Jimmy-Chu-127/Pinball-Machine-Built-from-Scratch/images/block_diagram_pinball_machine.png

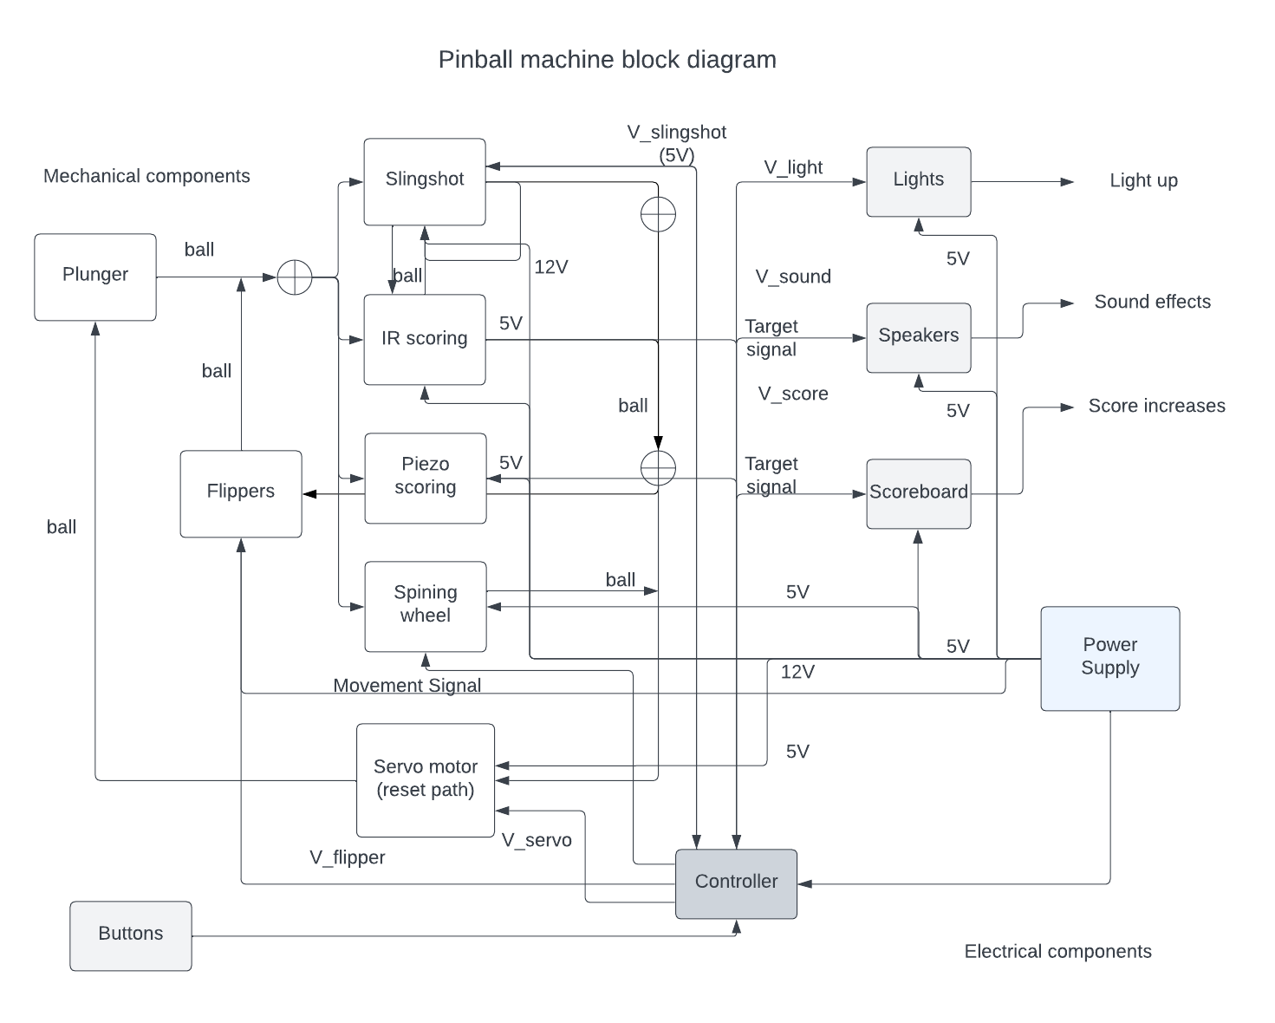
images/block_diagram_pinball_machine.png
