Jimmy-Chu-127/Pinball-Machine-Built-from-Scratch/Module 4/smps-lrs-75-12-1.snapshot.1/SMPS SMALL_LRS-75-12.JPG

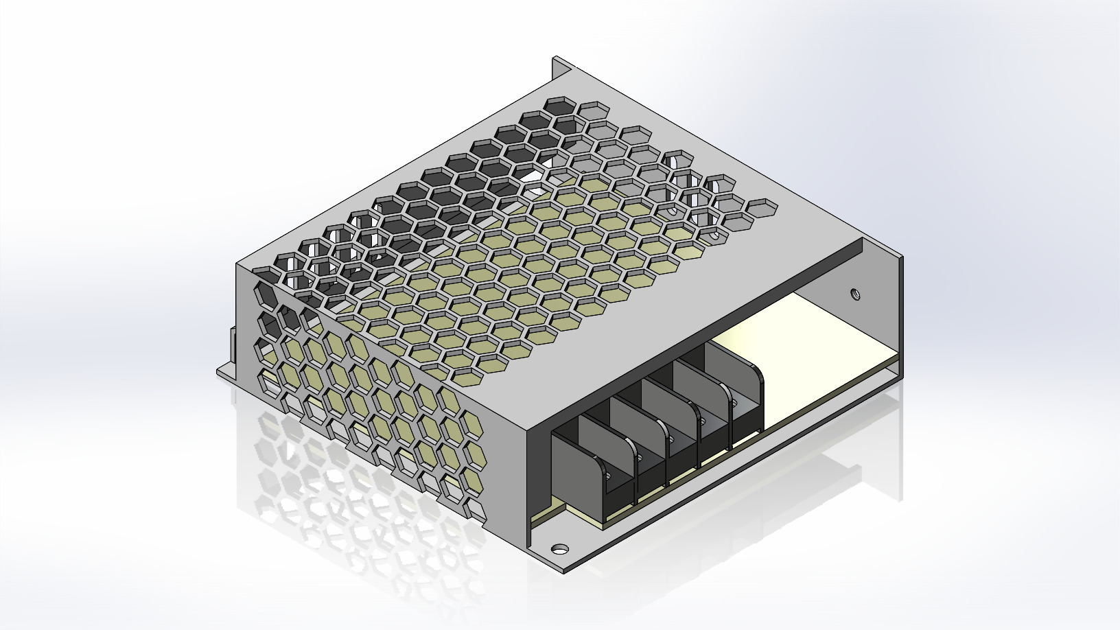
Module 4/smps-lrs-75-12-1.snapshot.1/SMPS SMALL_LRS-75-12.JPG
