Jimmy-Chu-127/Pinball-Machine-Built-from-Scratch/Module 4/switch_button/Rocker switch 3pin_3.JPG

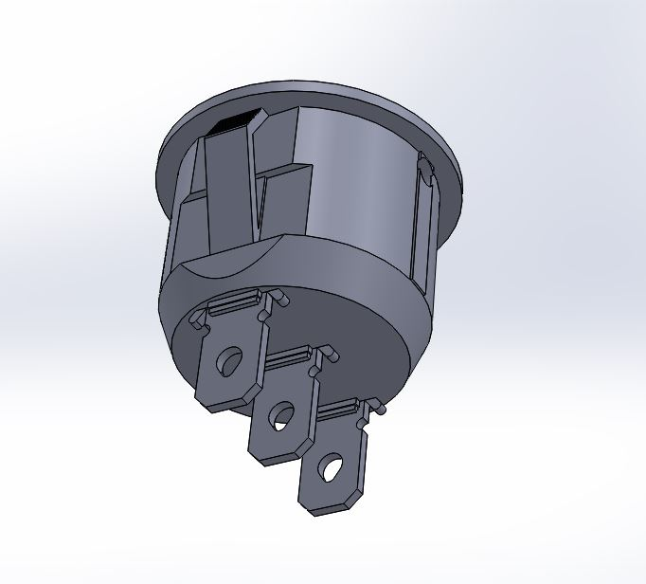
Module 4/switch_button/Rocker switch 3pin_3.JPG
