Jimmy-Chu-127/Pinball-Machine-Built-from-Scratch/Module 2/slingshot assem.SLDASM

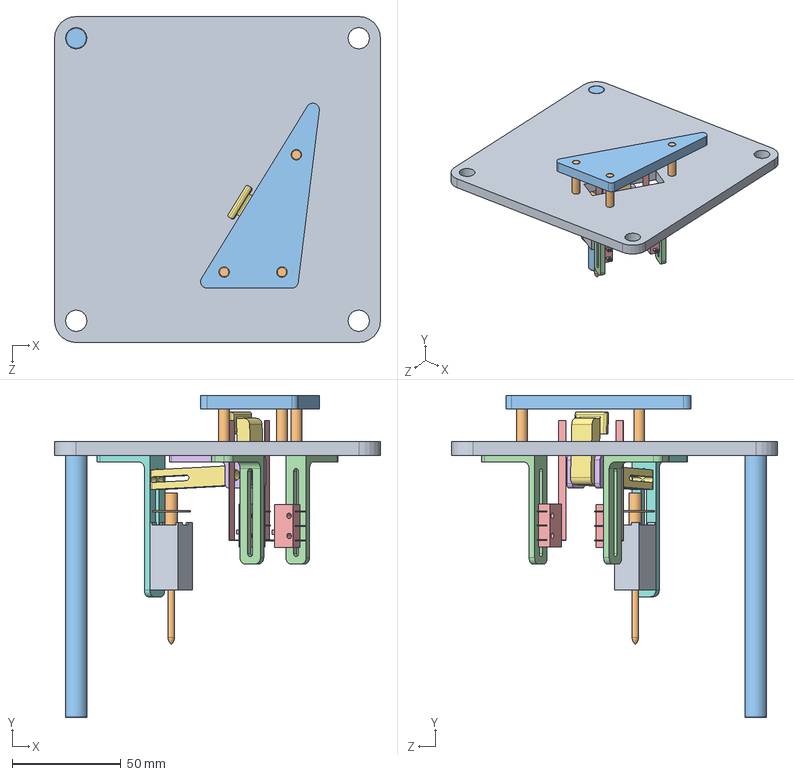
[picture p46: CAD file, 2023-05-12]
Module 2/slingshot assem.SLDASM
150.0 x 148.4 x 150.0 mm
slingshot testbed v2
slingshot support rod x 3
slingshot cover
slingshot limit switch holder x 2
slingshot limit switch x 2
slingshot arm holder
slingshot arm
slingshot solenoid holder vertical
slingshot solenoid body
slingshot solenoid rod
