Jimmy-Chu-127/Pinball-Machine-Built-from-Scratch/Module 1/plunger_assembly1_spring_head_rod.stl

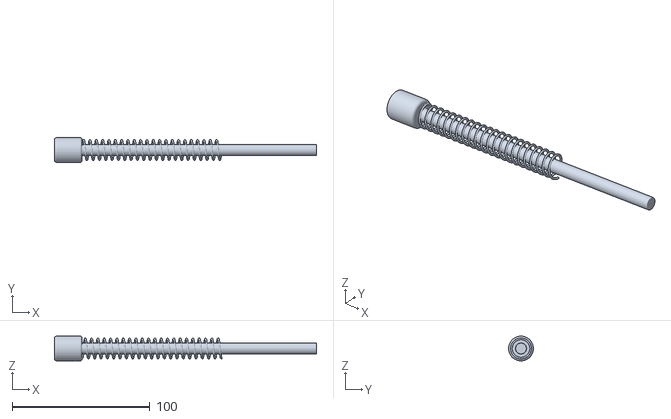
[picture p47: CAD file, 2023-04-08]
Module 1/plunger_assembly1_spring_head_rod.stl
190.0 x 18.0 x 18.0
