Jimmy-Chu-127/Pinball-Machine-Built-from-Scratch/Module 4/AL6M-M14G.SLDASM

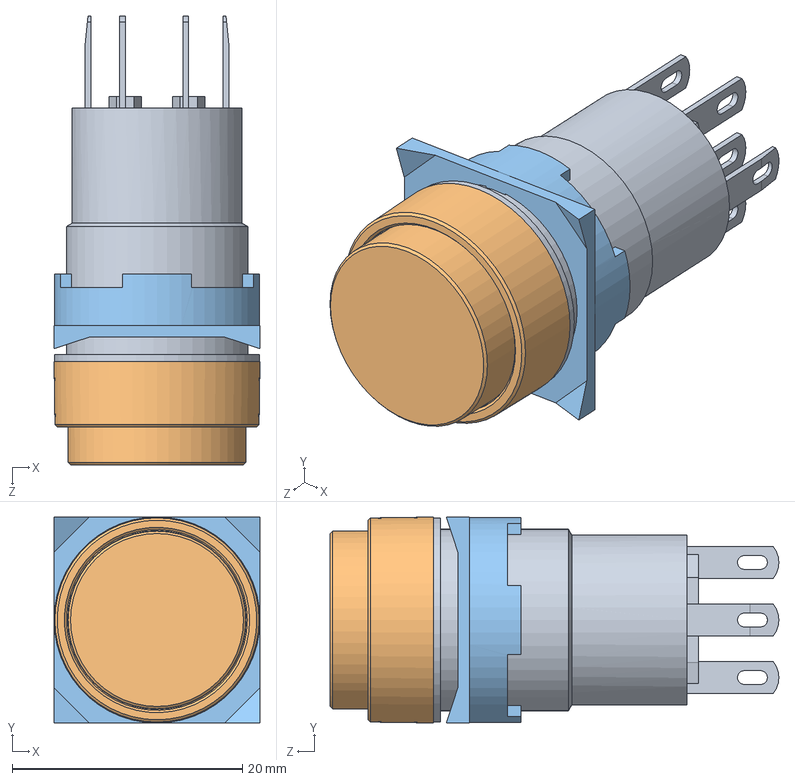
[picture p48: CAD file, 2023-05-24]
Module 4/AL6M-M14G.SLDASM
17.9 x 17.9 x 39.0 mm
AL6M-M14G
_A6LM-M14G_round
_A6LM-M14_nut_set
