Jimmy-Chu-127/Pinball-Machine-Built-from-Scratch/Module 2/flipper_assem1.SLDASM

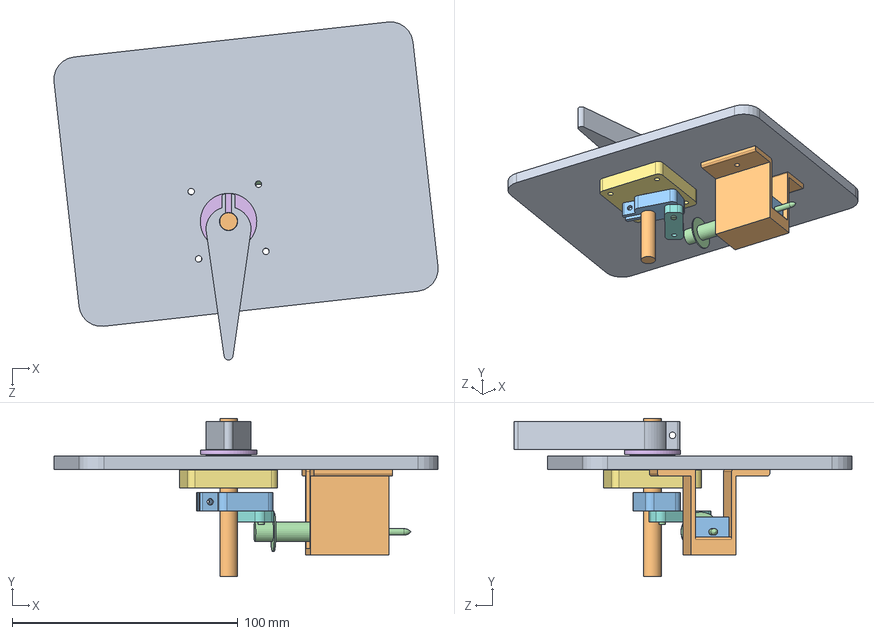
[picture p49: CAD file, 2023-04-26]
Module 2/flipper_assem1.SLDASM
170.1 x 70.0 x 149.7 mm
flipper_part1
flipper_part2
flipper_part3
flipper_part4
flipper_bearing
flipper_washer
flipper_part5
flipper_part6
plane
solenoid_holder
solenoid body
solenoid rod
