Jimmy-Chu-127/Pinball-Machine-Built-from-Scratch/3D printer - Laser cutting/5_21_print/3mf/ECE 115 Playfield spinning wheel.3mf

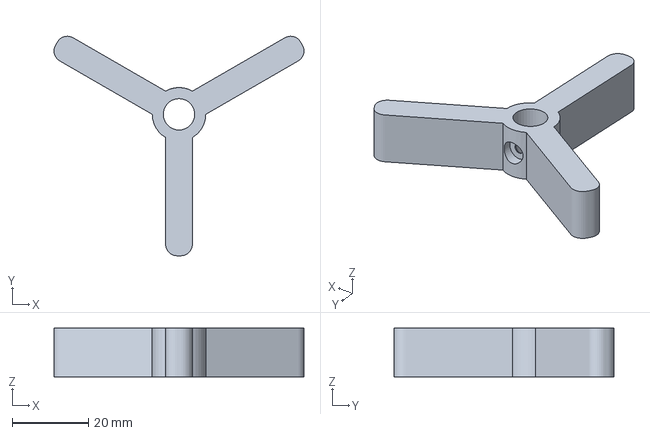
[picture p50: CAD file, 2023-05-22]
3D printer - Laser cutting/5_21_print/3mf/ECE 115 Playfield spinning wheel.3mf
65.4 x 57.4 x 12.7 mm
