Jimmy-Chu-127/Pinball-Machine-Built-from-Scratch/3D printer - Laser cutting/5_24_print/3mf/slingshot arm rotate rod large.3mf

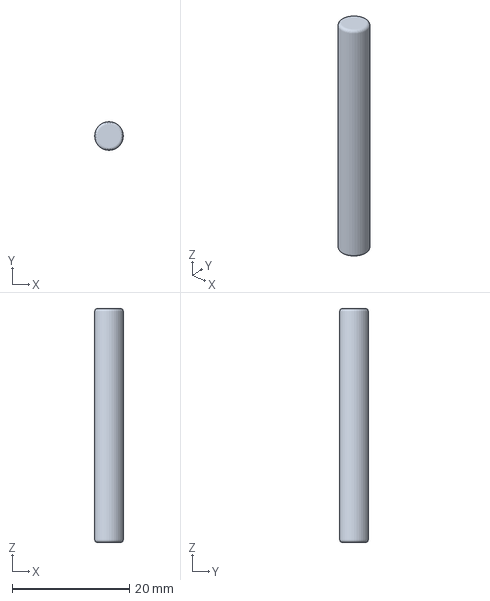
[picture p52: CAD file, 2023-05-24]
3D printer - Laser cutting/5_24_print/3mf/slingshot arm rotate rod large.3mf
4.90 x 4.90 x 40.0 mm
