Jimmy-Chu-127/Pinball-Machine-Built-from-Scratch/Module 1/HC/Tutor2.SLDPRT

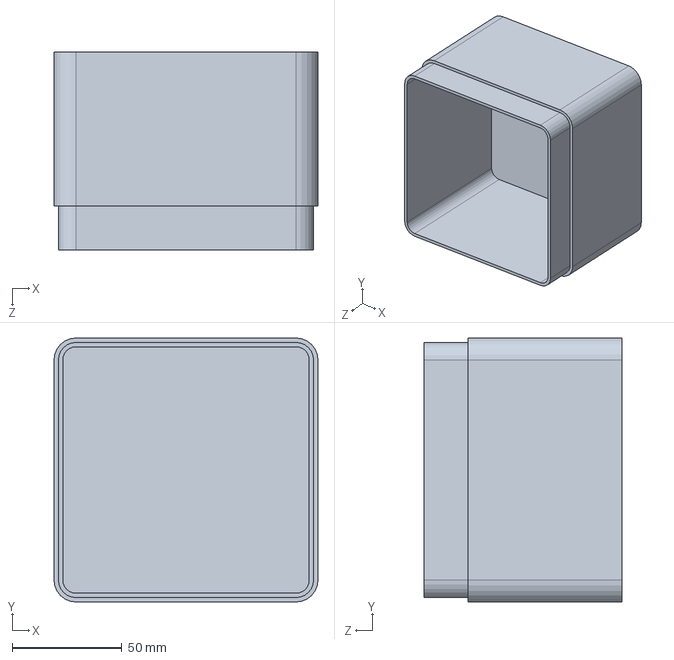
[picture p53: CAD file, 2023-04-07]
Module 1/HC/Tutor2.SLDPRT
120.0 x 120.0 x 90.0 mm
