Jimmy-Chu-127/Pinball-Machine-Built-from-Scratch/Module 2/ECE 115 spin wheel testbed.SLDPRT

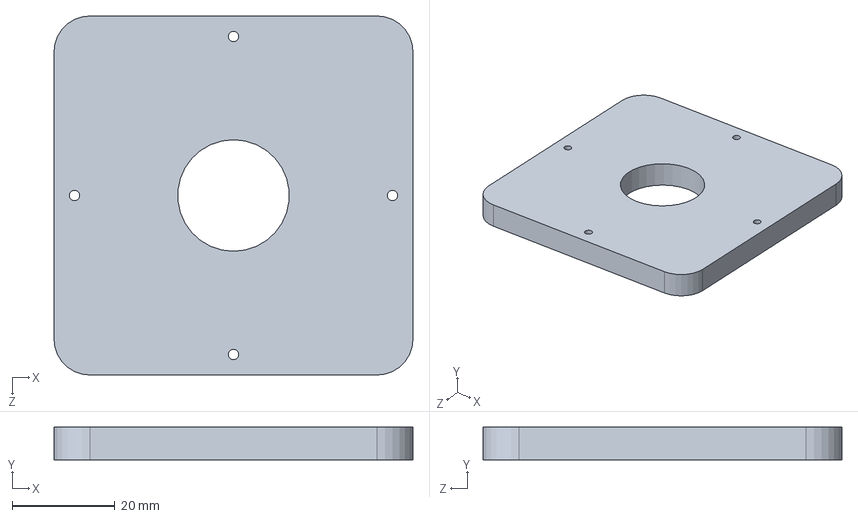
[picture p54: CAD file, 2023-05-24]
Module 2/ECE 115 spin wheel testbed.SLDPRT
70.0 x 6.35 x 70.0 mm
