Jimmy-Chu-127/Pinball-Machine-Built-from-Scratch/Module 3/IR mount x2.3mf

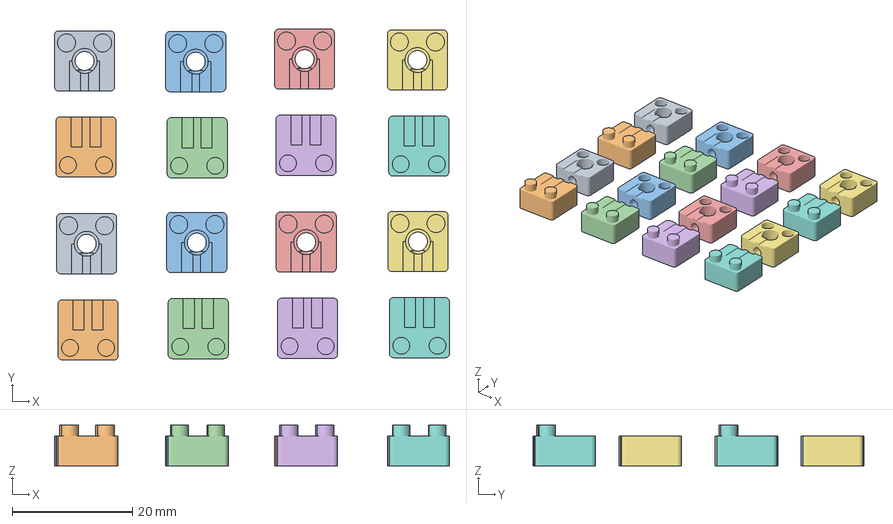
[picture p55: CAD file, 2023-05-22]
Module 3/IR mount x2.3mf
65.6 x 55.0 x 6.80 mm
IR mount 1.STL x 8
IR mount 2.STL x 8
