Jimmy-Chu-127/Pinball-Machine-Built-from-Scratch/Module 4/display/display_board1.SLDPRT

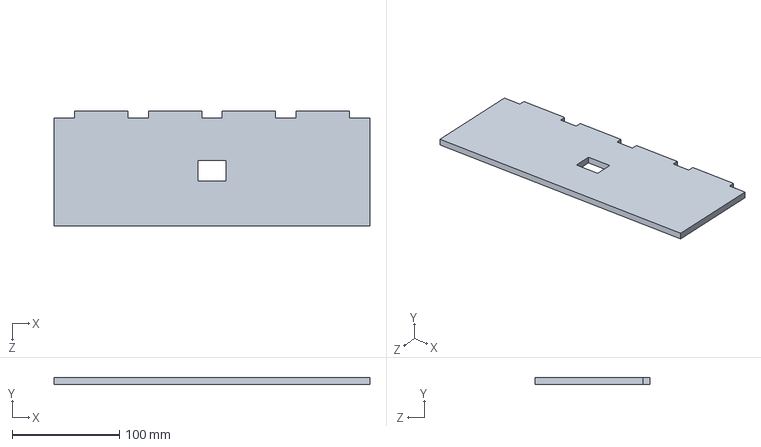
[picture p56: CAD file, 2023-05-24]
Module 4/display/display_board1.SLDPRT
295.0 x 6.35 x 107.4 mm
