Jimmy-Chu-127/Pinball-Machine-Built-from-Scratch/Module 4/flipper_update/flipper_part6.SLDPRT

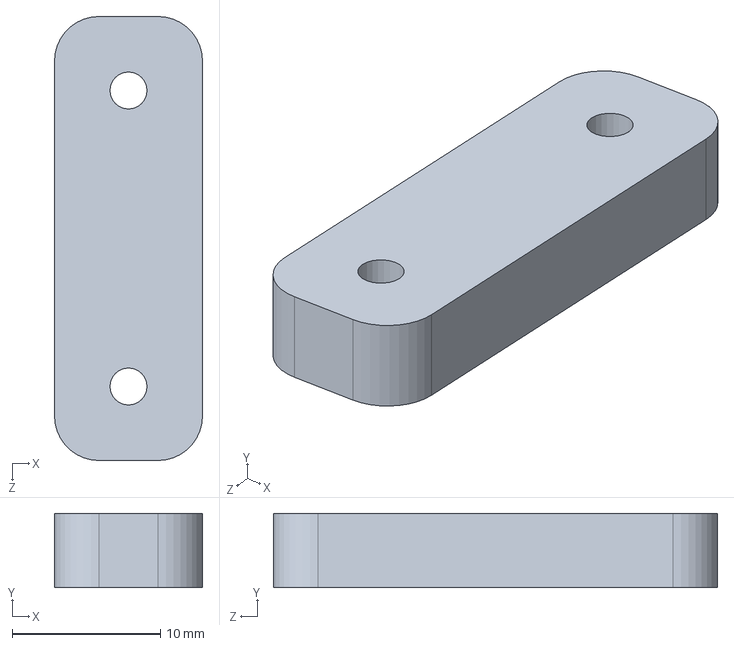
[picture p57: CAD file, 2023-05-31]
Module 4/flipper_update/flipper_part6.SLDPRT
10.0 x 5.00 x 30.0 mm
