Jimmy-Chu-127/Pinball-Machine-Built-from-Scratch/Module 4/piezo_cad/piezo_sensor.SLDPRT

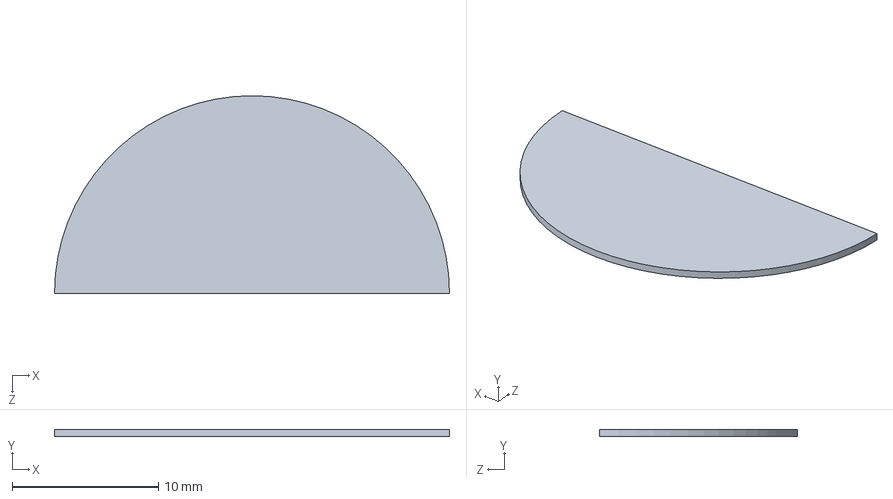
[picture p58: CAD file, 2023-05-21]
Module 4/piezo_cad/piezo_sensor.SLDPRT
27.0 x 0.5 x 13.5 mm
