Jimmy-Chu-127/Pinball-Machine-Built-from-Scratch/Module 4/plunger_update/plunger_head2.SLDPRT

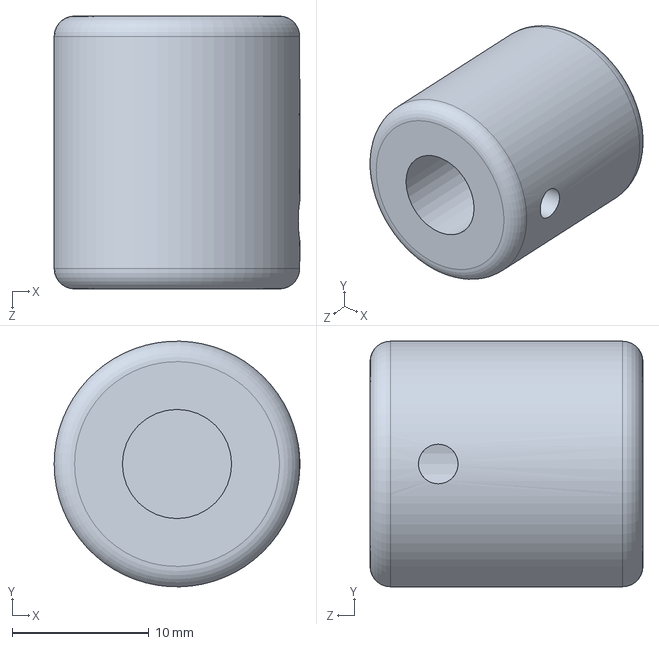
[picture p59: CAD file, 2023-05-23]
Module 4/plunger_update/plunger_head2.SLDPRT
18.0 x 18.0 x 20.0 mm
