Jimmy-Chu-127/Pinball-Machine-Built-from-Scratch/Module 4/smps-lrs-75-12-1.snapshot.1/SMPS SMALL_LRS-75-12.STEP

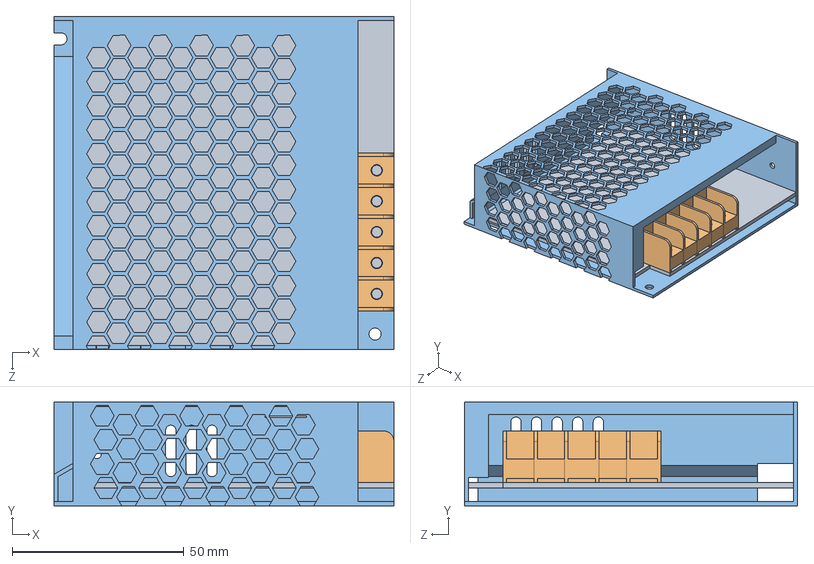
[picture p60: CAD file, 2023-05-23]
Module 4/smps-lrs-75-12-1.snapshot.1/SMPS SMALL_LRS-75-12.STEP
99.0 x 30.2 x 97.0 mm
