Jimmy-Chu-127/Pinball-Machine-Built-from-Scratch/Module 4/switch_button/Rocker switch 3pin.SLDPRT

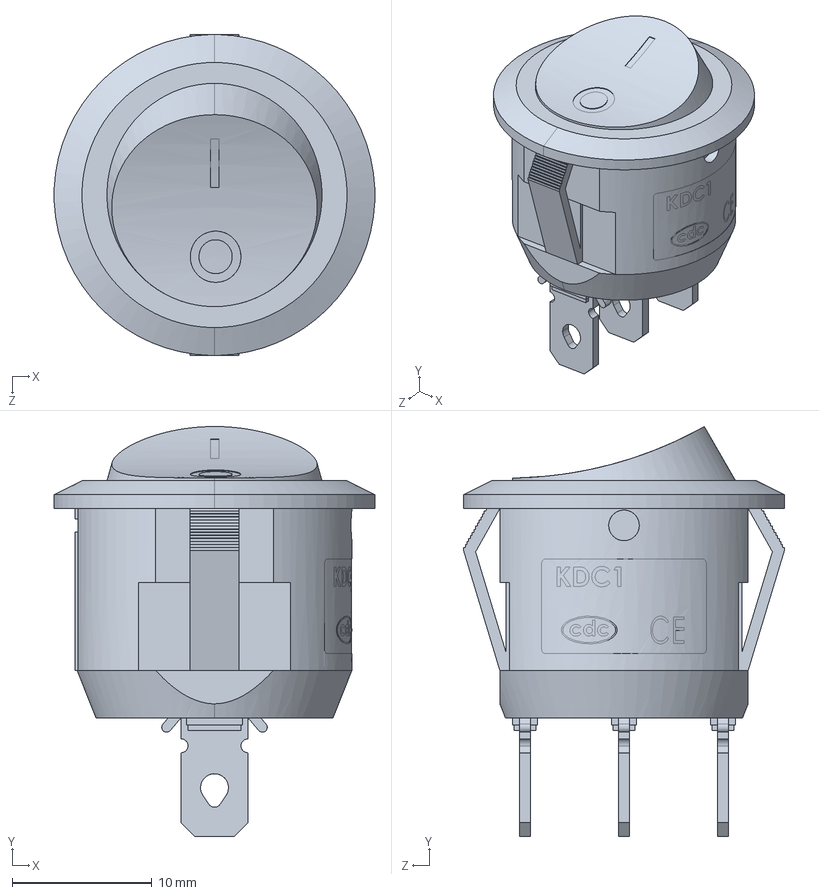
[picture p61: CAD file, 2023-05-23]
Module 4/switch_button/Rocker switch 3pin.SLDPRT
23.0 x 29.4 x 23.0 mm
