Jimmy-Chu-127/Pinball-Machine-Built-from-Scratch/3D printer - Laser cutting/5_21_print/3mf/ECE 115 spin wheel connector.3mf

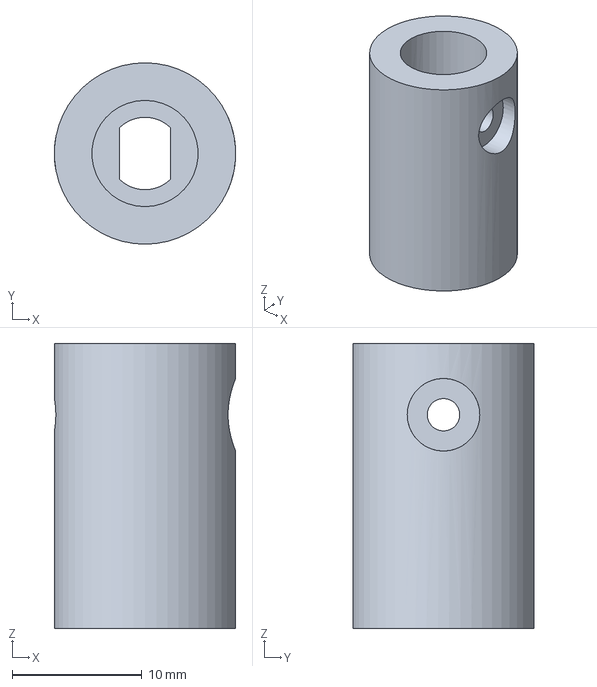
[picture p62: CAD file, 2023-05-22]
3D printer - Laser cutting/5_21_print/3mf/ECE 115 spin wheel connector.3mf
14.0 x 14.0 x 22.0 mm
