Jimmy-Chu-127/Pinball-Machine-Built-from-Scratch/3D printer - Laser cutting/5_24_print/3mf/slingshot arm holder large.3mf

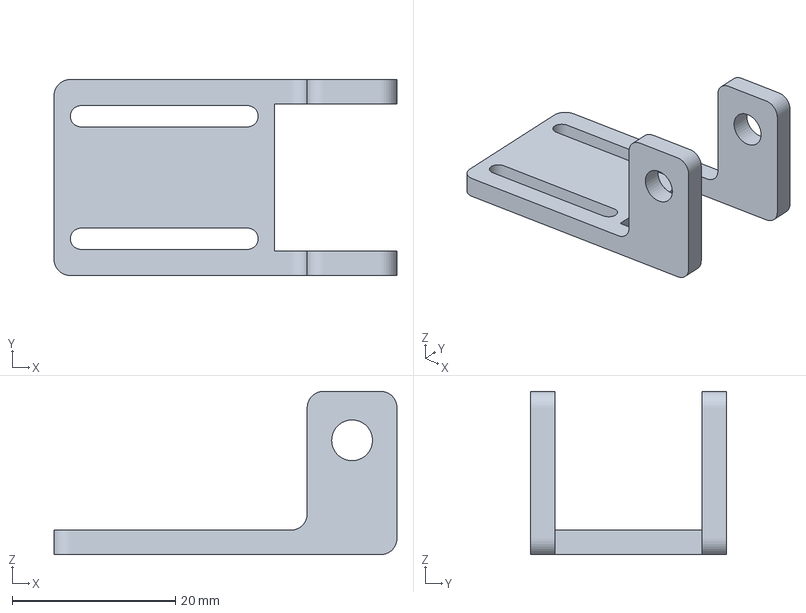
[picture p64: CAD file, 2023-05-24]
3D printer - Laser cutting/5_24_print/3mf/slingshot arm holder large.3mf
42.0 x 24.0 x 20.0 mm
