Jimmy-Chu-127/Pinball-Machine-Built-from-Scratch/Module 1/ECE 115 Module 1 plunger handle v2.SLDPRT

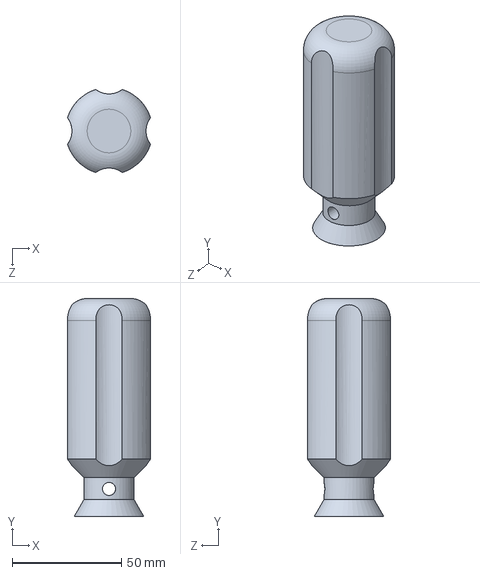
[picture p65: CAD file, 2023-04-09]
Module 1/ECE 115 Module 1 plunger handle v2.SLDPRT
38.1 x 100.0 x 38.1 mm
