Jimmy-Chu-127/Pinball-Machine-Built-from-Scratch/Module 2 revision/slingshot testbed v3.SLDPRT

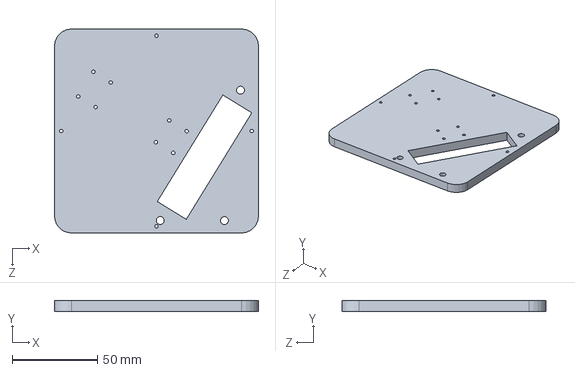
[picture p66: CAD file, 2023-05-24]
Module 2 revision/slingshot testbed v3.SLDPRT
120.0 x 6.35 x 120.0 mm
