Jimmy-Chu-127/Pinball-Machine-Built-from-Scratch/Module 4/piezo_cad/piezo_sensor_testbed.SLDPRT

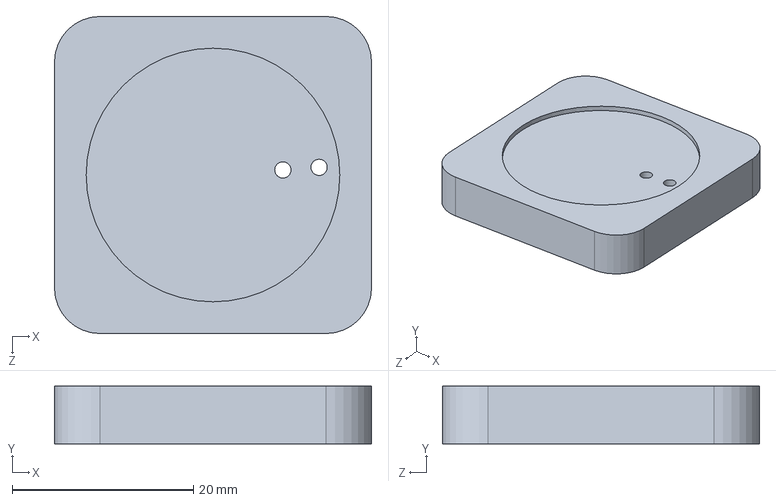
[picture p67: CAD file, 2023-05-14]
Module 4/piezo_cad/piezo_sensor_testbed.SLDPRT
35.0 x 6.35 x 35.0 mm
