Jimmy-Chu-127/Pinball-Machine-Built-from-Scratch/3D printer - Laser cutting/5_21_print/3mf/ECE 115 spin wheel holder side.3mf

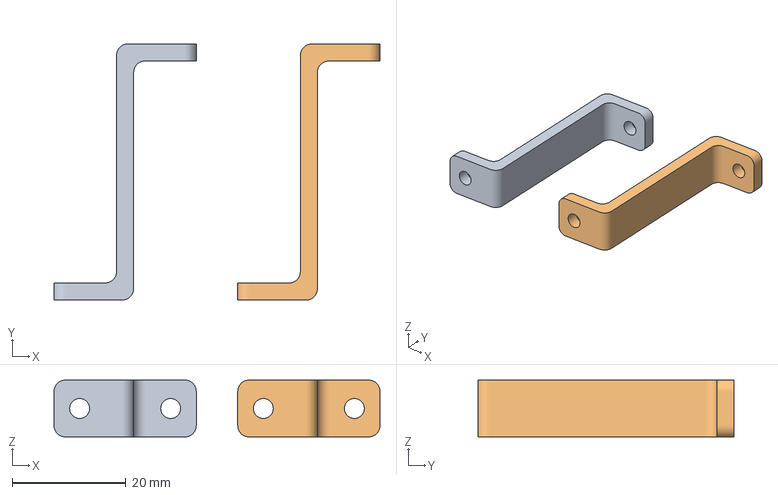
[picture p68: CAD file, 2023-05-22]
3D printer - Laser cutting/5_21_print/3mf/ECE 115 spin wheel holder side.3mf
57.3 x 45.0 x 10.0 mm
ECE 115 spin wheel holder side.STL x 2
