Jimmy-Chu-127/Pinball-Machine-Built-from-Scratch/3D printer - Laser cutting/5_24_cut/DXF/playfield v2.DXF

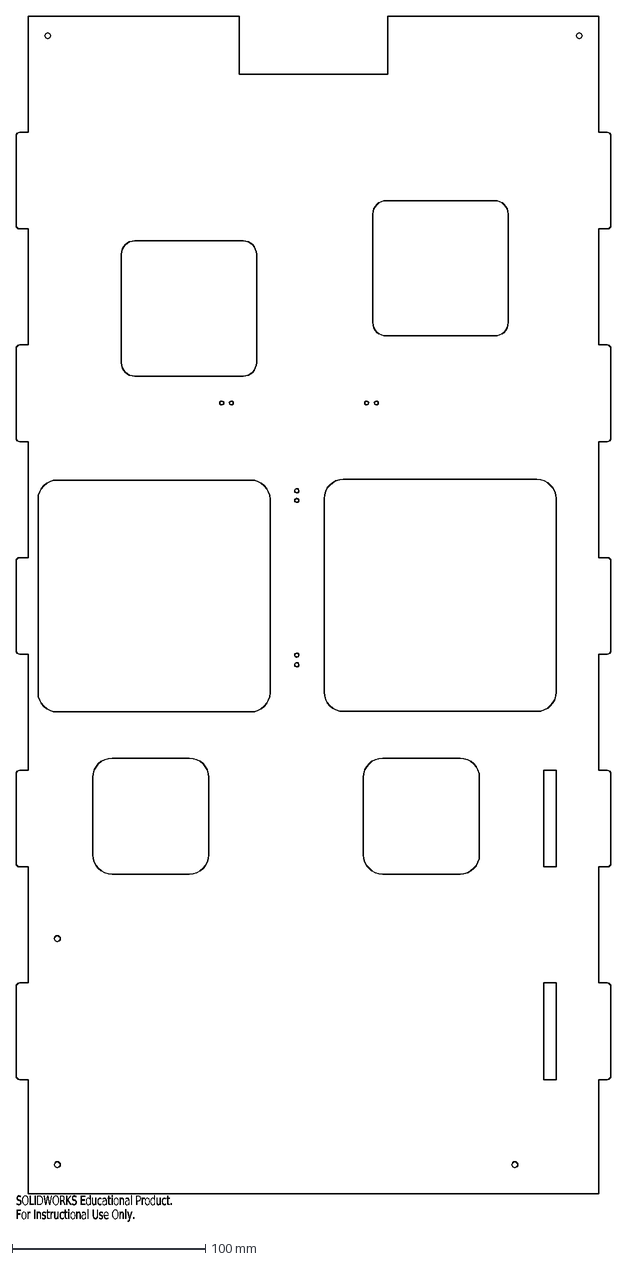
[picture p69: CAD file, 2023-05-24]
3D printer - Laser cutting/5_24_cut/DXF/playfield v2.DXF
SOLIDWORKS Educational Product.
For Instructional Use Only.
