Jimmy-Chu-127/Pinball-Machine-Built-from-Scratch/3D printer - Laser cutting/5_24_print/3mf/slingshot rotate locker.3mf

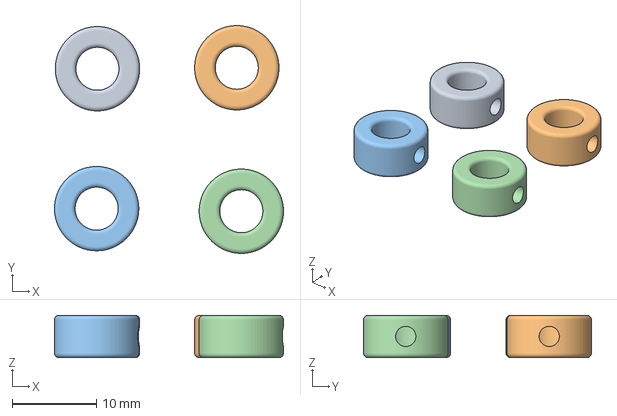
[picture p70: CAD file, 2023-05-24]
3D printer - Laser cutting/5_24_print/3mf/slingshot rotate locker.3mf
27.2 x 27.0 x 5.00 mm
slingshot rotate locker.STL x 4
