Jimmy-Chu-127/Pinball-Machine-Built-from-Scratch/Module 1/plunger_spring2.SLDPRT

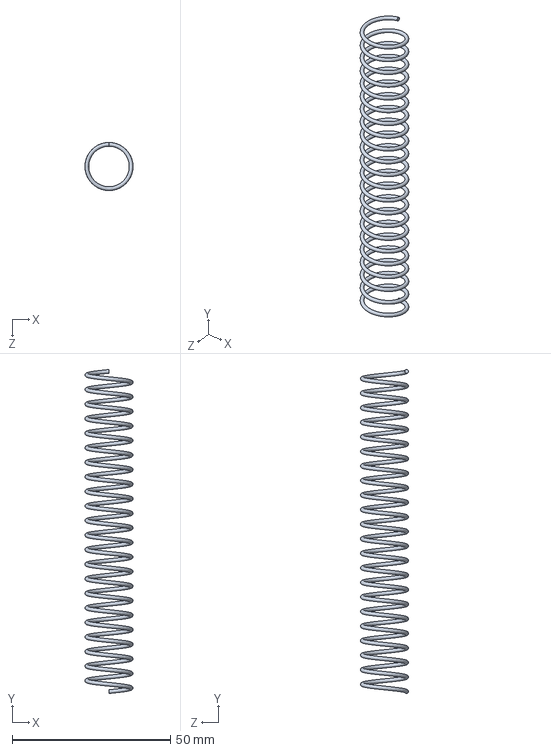
[picture p71: CAD file, 2023-04-09]
Module 1/plunger_spring2.SLDPRT
15.2 x 102.4 x 15.2 mm
