Jimmy-Chu-127/Pinball-Machine-Built-from-Scratch/Module 3/IR mount testbed.SLDPRT

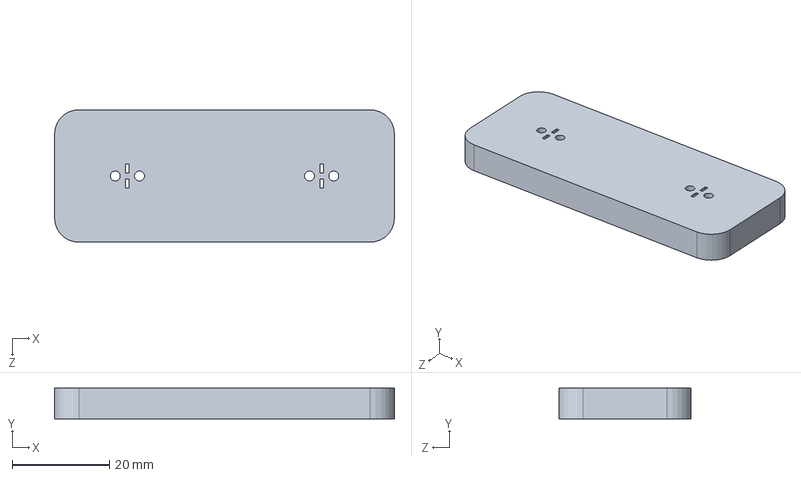
[picture p72: CAD file, 2023-05-12]
Module 3/IR mount testbed.SLDPRT
70.0 x 6.35 x 27.3 mm
