Jimmy-Chu-127/Pinball-Machine-Built-from-Scratch/Module 4/display/display_board3.SLDPRT

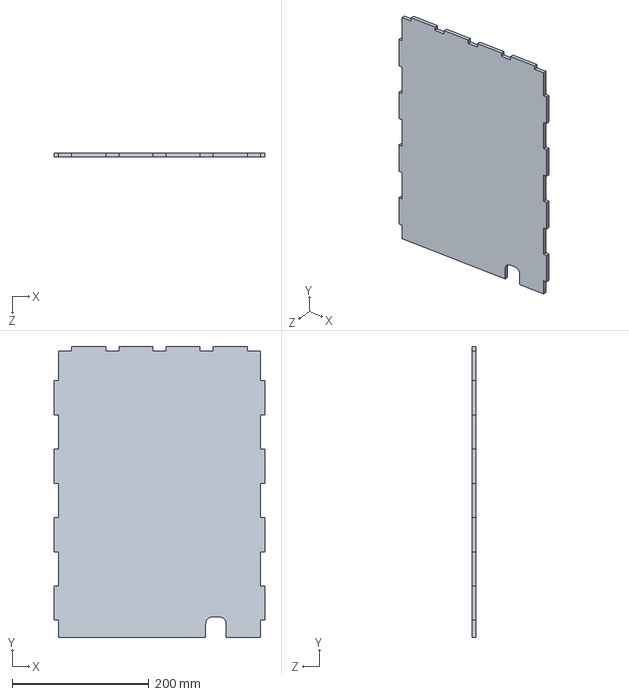
[picture p73: CAD file, 2023-05-24]
Module 4/display/display_board3.SLDPRT
307.7 x 425.3 x 6.35 mm
