Jimmy-Chu-127/Pinball-Machine-Built-from-Scratch/Module 4/surface_p1_tap.SLDPRT

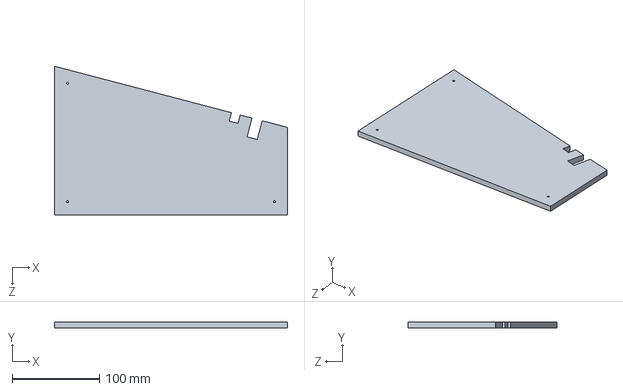
[picture p74: CAD file, 2023-05-31]
Module 4/surface_p1_tap.SLDPRT
266.6 x 6.35 x 170.0 mm
