Jimmy-Chu-127/Pinball-Machine-Built-from-Scratch/3D printer - Laser cutting/5_24_cut/DXF/surface_p3.DXF

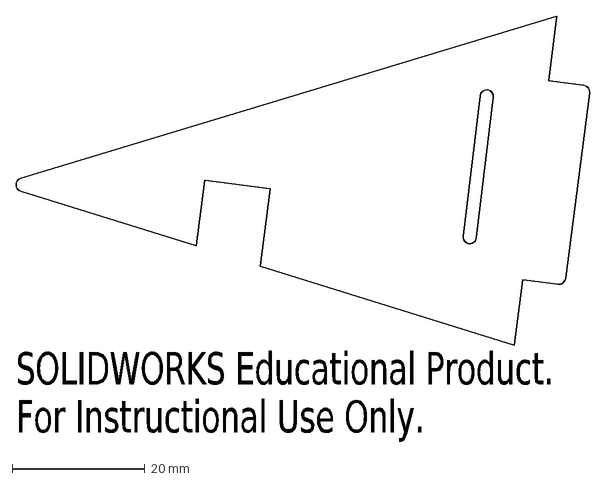
[picture p75: CAD file, 2023-05-24]
3D printer - Laser cutting/5_24_cut/DXF/surface_p3.DXF
SOLIDWORKS Educational Product.
For Instructional Use Only.
