Jimmy-Chu-127/Pinball-Machine-Built-from-Scratch/Module 1/plunger_head.sldprt

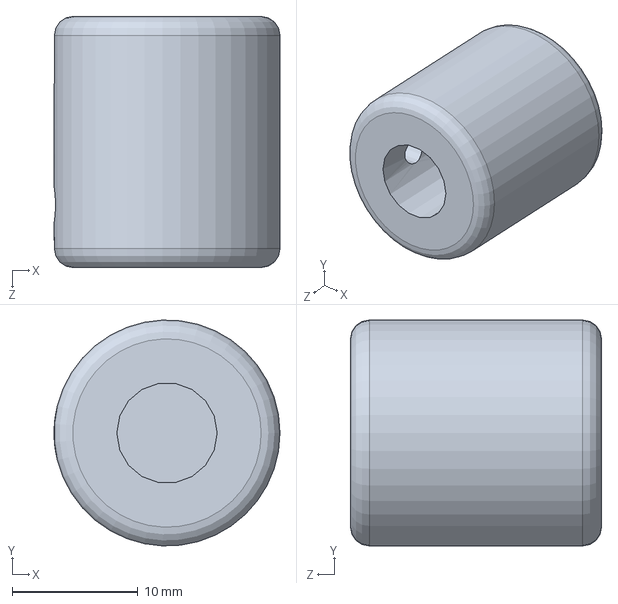
[picture p76: CAD file, 2023-04-09]
Module 1/plunger_head.sldprt
18.0 x 18.0 x 20.0 mm
