Jimmy-Chu-127/Pinball-Machine-Built-from-Scratch/Module 2/slingshot fit tester.SLDPRT

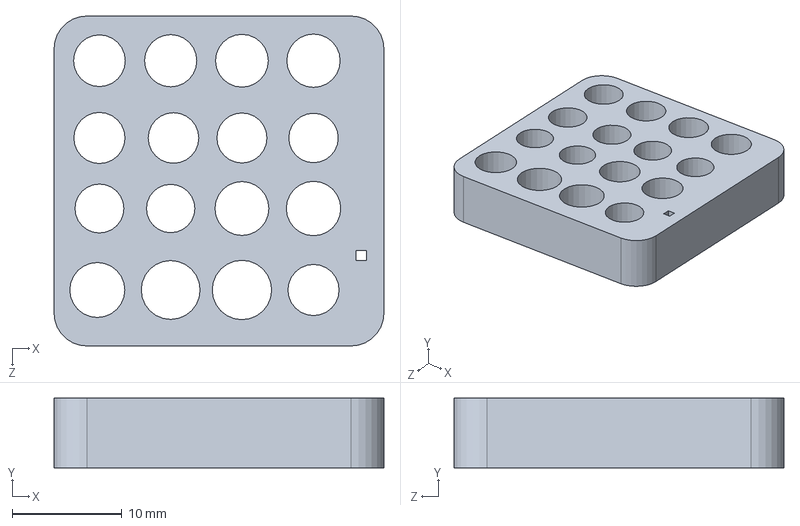
[picture p77: CAD file, 2023-05-17]
Module 2/slingshot fit tester.SLDPRT
30.0 x 6.35 x 30.0 mm
