Jimmy-Chu-127/Pinball-Machine-Built-from-Scratch/Module 3/IR mount 1.SLDPRT

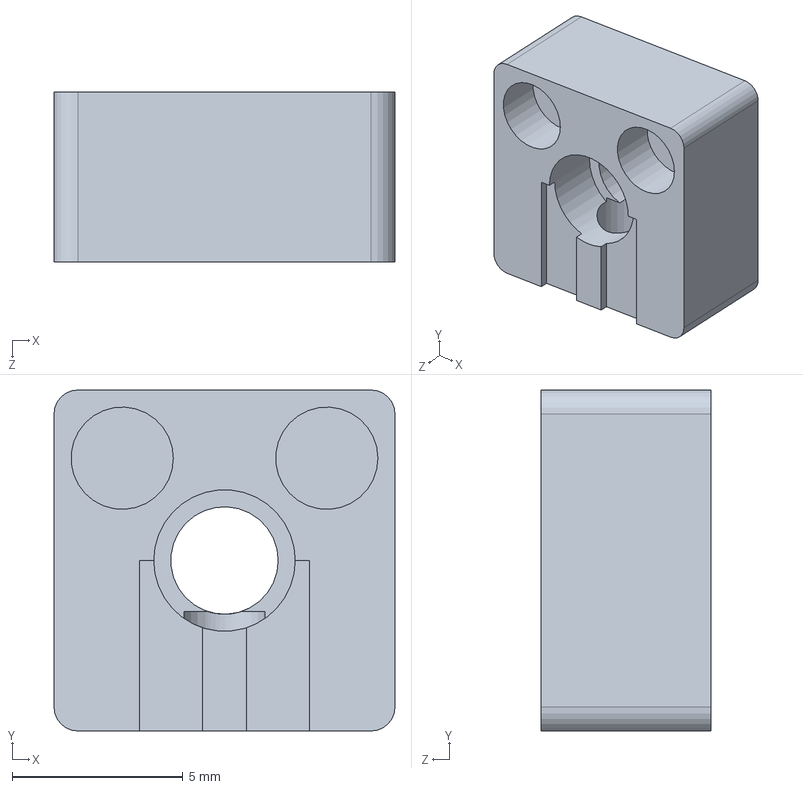
[picture p78: CAD file, 2023-05-09]
Module 3/IR mount 1.SLDPRT
10.0 x 10.0 x 5.00 mm
