Jimmy-Chu-127/Pinball-Machine-Built-from-Scratch/Module 4/display/display_board2.SLDPRT

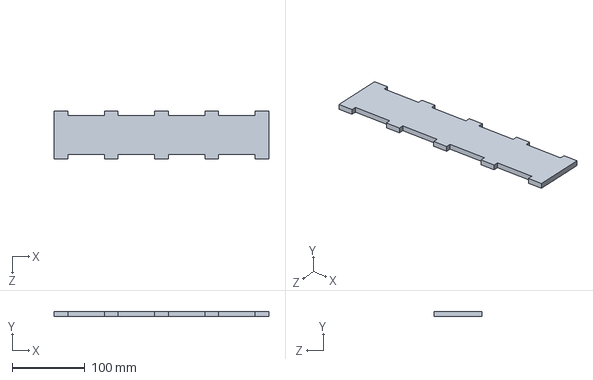
[picture p79: CAD file, 2023-05-22]
Module 4/display/display_board2.SLDPRT
295.0 x 6.35 x 66.3 mm
