Jimmy-Chu-127/Pinball-Machine-Built-from-Scratch/Module 4/flipper_update/plane.SLDPRT

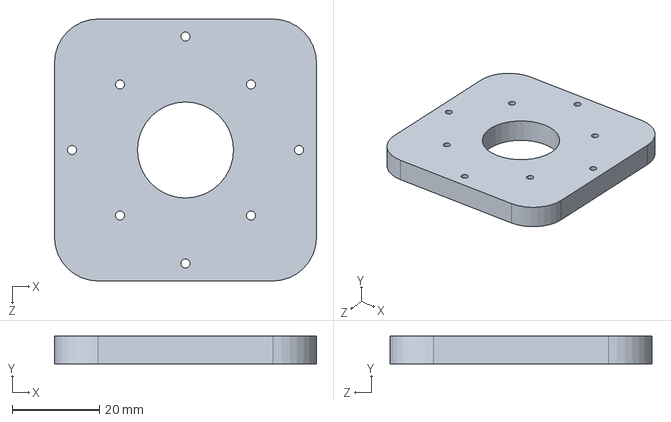
[picture p80: CAD file, 2023-05-24]
Module 4/flipper_update/plane.SLDPRT
60.0 x 6.35 x 60.0 mm
