Jimmy-Chu-127/Pinball-Machine-Built-from-Scratch/Module 4/plunger_update/plunger_spring2.SLDPRT

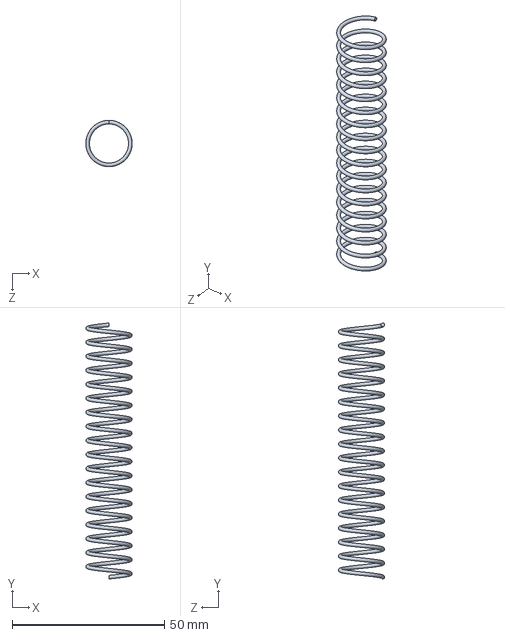
[picture p81: CAD file, 2023-05-23]
Module 4/plunger_update/plunger_spring2.SLDPRT
15.2 x 84.0 x 15.2 mm
