Jimmy-Chu-127/Pinball-Machine-Built-from-Scratch/Module 4/surface_p2.SLDPRT

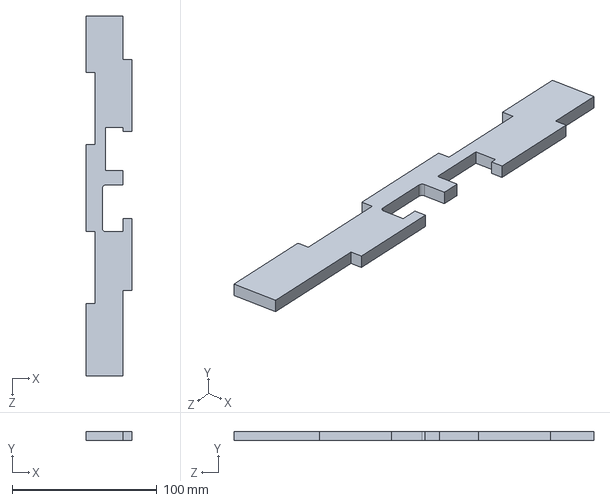
[picture p82: CAD file, 2023-05-31]
Module 4/surface_p2.SLDPRT
31.8 x 6.35 x 249.0 mm
