Jimmy-Chu-127/Pinball-Machine-Built-from-Scratch/Module 1/HC/Pressure Plate.SLDPRT

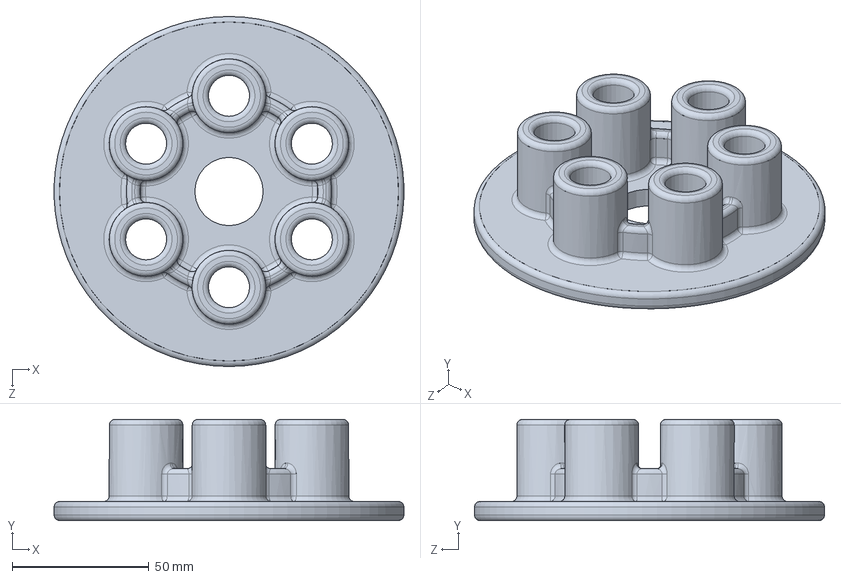
[picture p84: CAD file, 2023-04-07]
Module 1/HC/Pressure Plate.SLDPRT
127.9 x 37.0 x 128.0 mm
