Jimmy-Chu-127/Pinball-Machine-Built-from-Scratch/Module 3/IR mount 2.SLDPRT

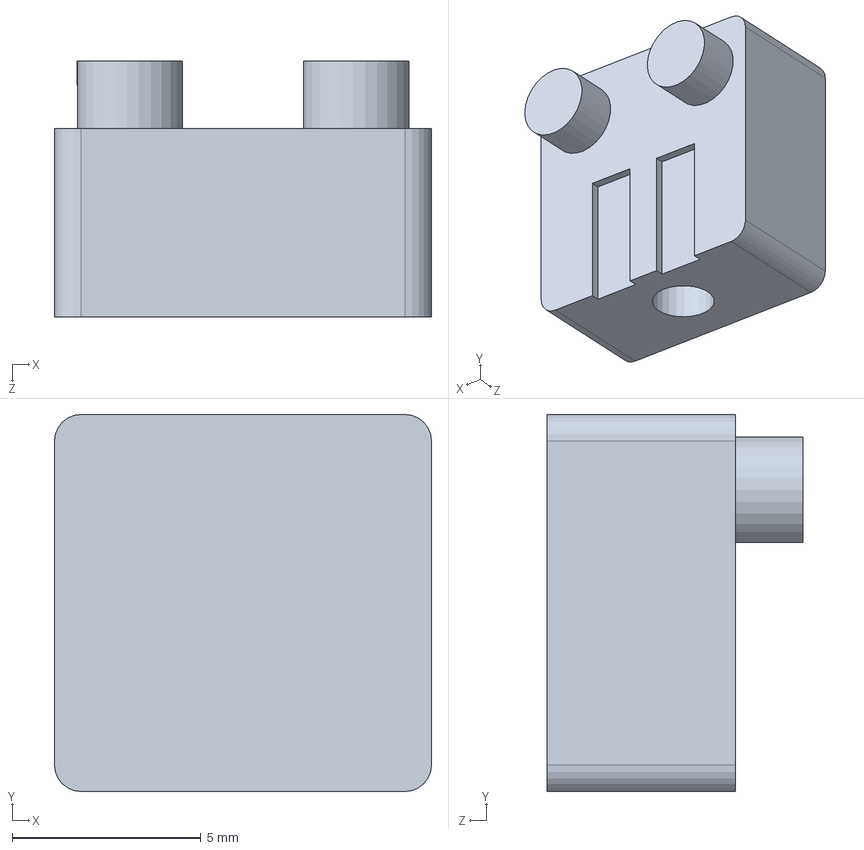
[picture p85: CAD file, 2023-05-09]
Module 3/IR mount 2.SLDPRT
10.0 x 10.0 x 6.80 mm
