Jimmy-Chu-127/Pinball-Machine-Built-from-Scratch/Module 4/display/7segment_display.SLDPRT

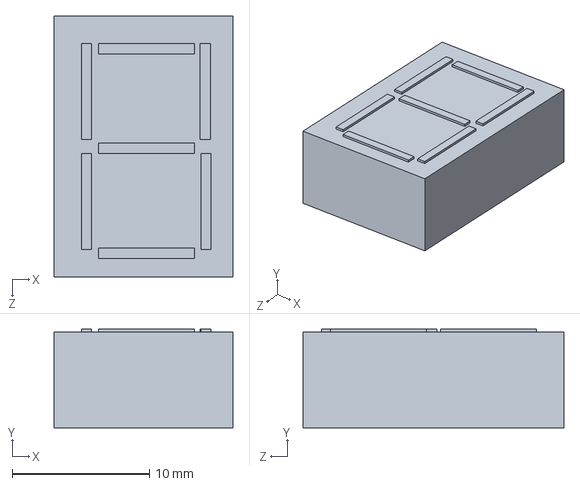
[picture p86: CAD file, 2023-05-22]
Module 4/display/7segment_display.SLDPRT
13.0 x 7.20 x 19.0 mm
