Jimmy-Chu-127/Pinball-Machine-Built-from-Scratch/Module 4/flipper_update/solenoid_holder2.SLDPRT

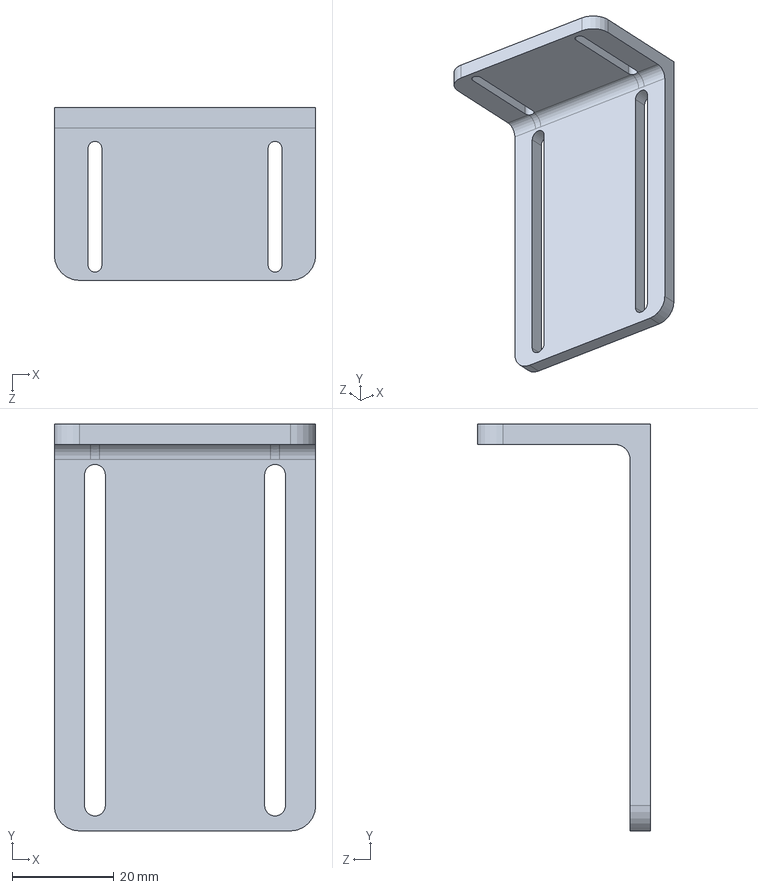
[picture p87: CAD file, 2023-05-22]
Module 4/flipper_update/solenoid_holder2.SLDPRT
51.4 x 80.0 x 34.0 mm
