Jimmy-Chu-127/Pinball-Machine-Built-from-Scratch/Module 4/plunger_update/plunger_rod2.SLDPRT

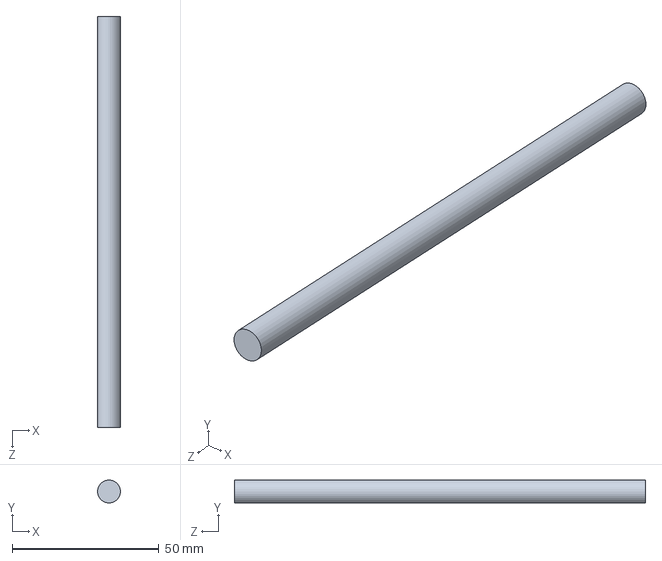
[picture p88: CAD file, 2023-05-23]
Module 4/plunger_update/plunger_rod2.SLDPRT
7.80 x 7.76 x 140.0 mm
