Jimmy-Chu-127/Pinball-Machine-Built-from-Scratch/3D printer - Laser cutting/5_24_cut/DXF/surface_left_side_panel.DXF

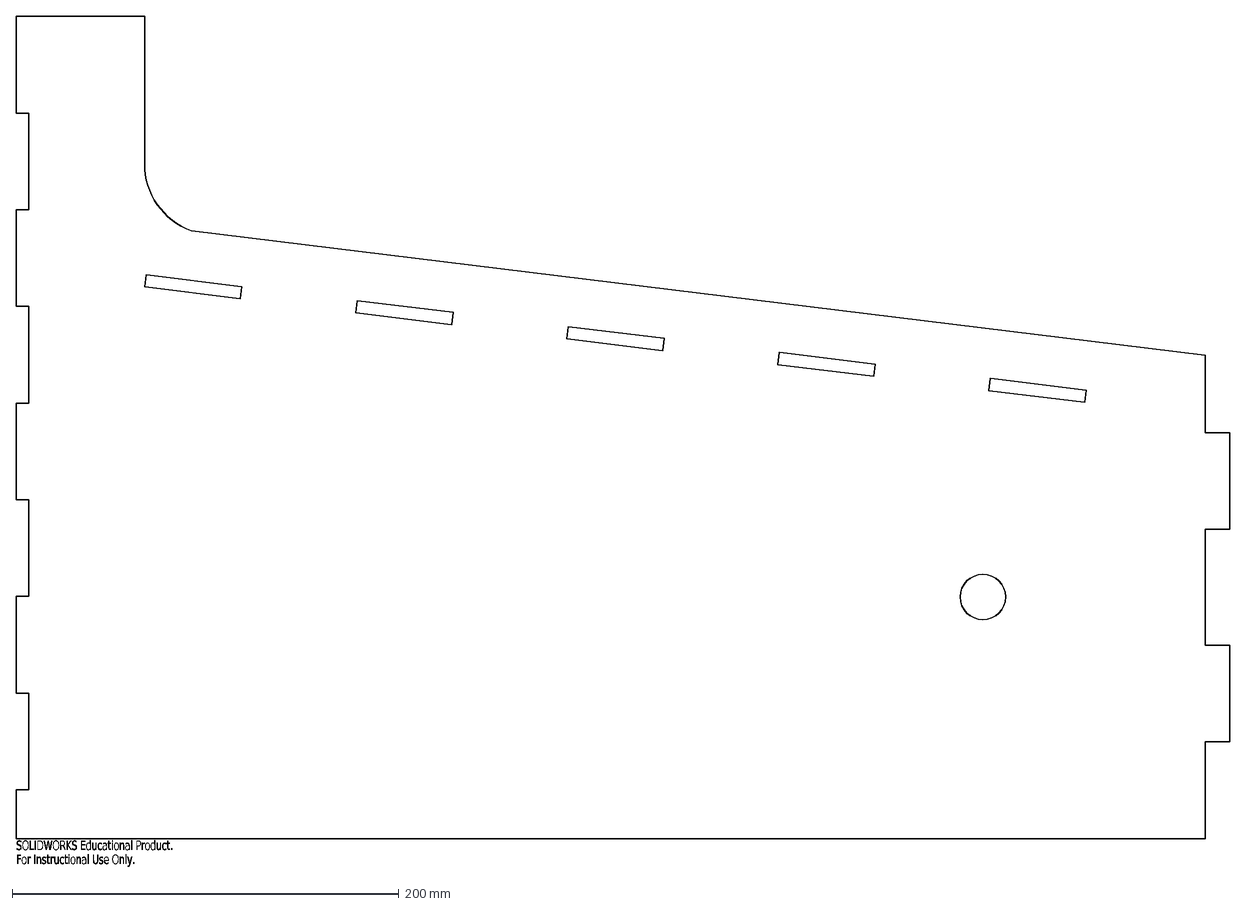
[picture p89: CAD file, 2023-05-24]
3D printer - Laser cutting/5_24_cut/DXF/surface_left_side_panel.DXF
SOLIDWORKS Educational Product.
For Instructional Use Only.
