Jimmy-Chu-127/Pinball-Machine-Built-from-Scratch/Module 1/HC/ECE 115 Module 1 part1 HC.SLDPRT

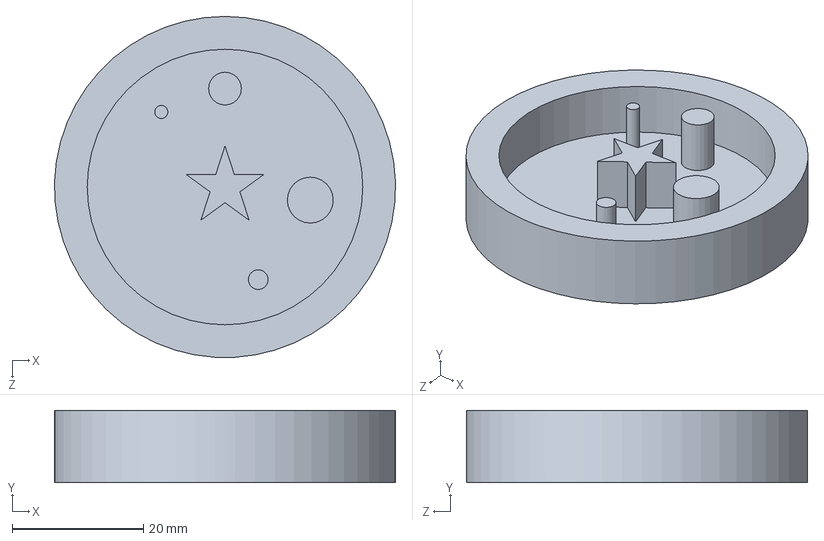
[picture p90: CAD file, 2023-04-07]
Module 1/HC/ECE 115 Module 1 part1 HC.SLDPRT
52.0 x 11.0 x 52.0 mm
