Jimmy-Chu-127/Pinball-Machine-Built-from-Scratch/Module 1/plunger_rod2.SLDPRT

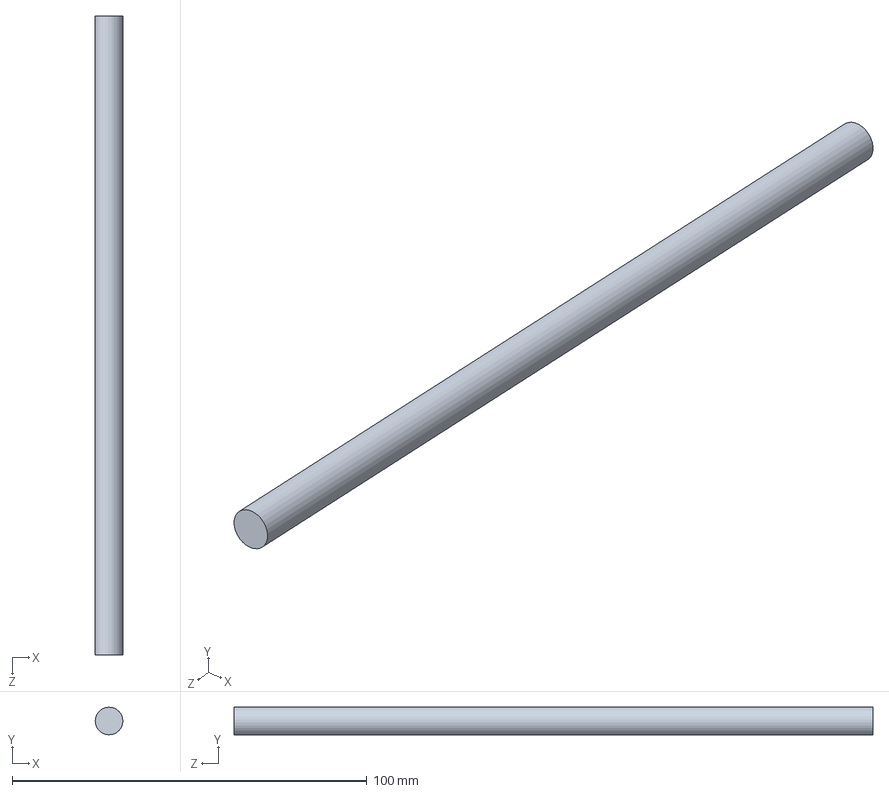
[picture p91: CAD file, 2023-04-09]
Module 1/plunger_rod2.SLDPRT
7.78 x 7.79 x 180.0 mm
