Jimmy-Chu-127/Pinball-Machine-Built-from-Scratch/Module 2/slingshot arm holder.SLDPRT

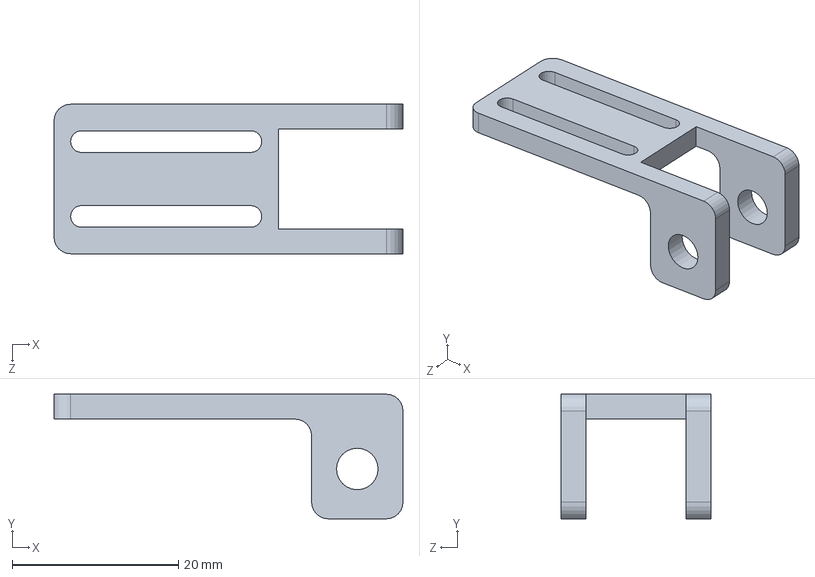
[picture p92: CAD file, 2023-05-12]
Module 2/slingshot arm holder.SLDPRT
42.0 x 15.0 x 18.0 mm
