Jimmy-Chu-127/Pinball-Machine-Built-from-Scratch/Module 3/display mount testbed.SLDPRT

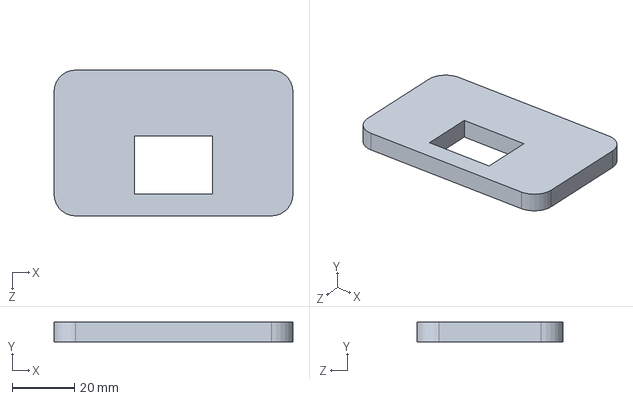
[picture p93: CAD file, 2023-05-09]
Module 3/display mount testbed.SLDPRT
77.0 x 6.35 x 47.0 mm
