Jimmy-Chu-127/Pinball-Machine-Built-from-Scratch/Module 4/flipper_update/flipper_part1.SLDPRT

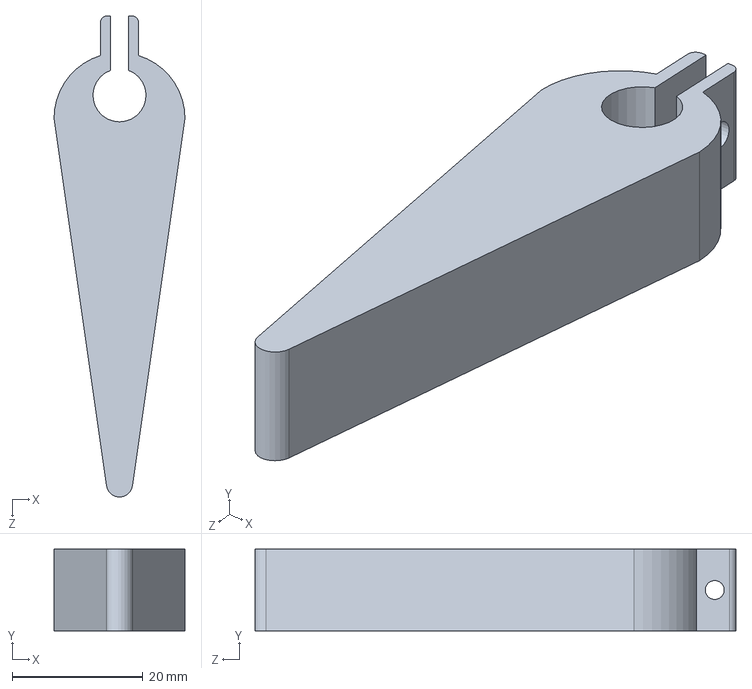
[picture p94: CAD file, 2023-05-21]
Module 4/flipper_update/flipper_part1.SLDPRT
20.0 x 12.5 x 73.5 mm
