Jimmy-Chu-127/Pinball-Machine-Built-from-Scratch/Module 4/surface_p3.SLDPRT

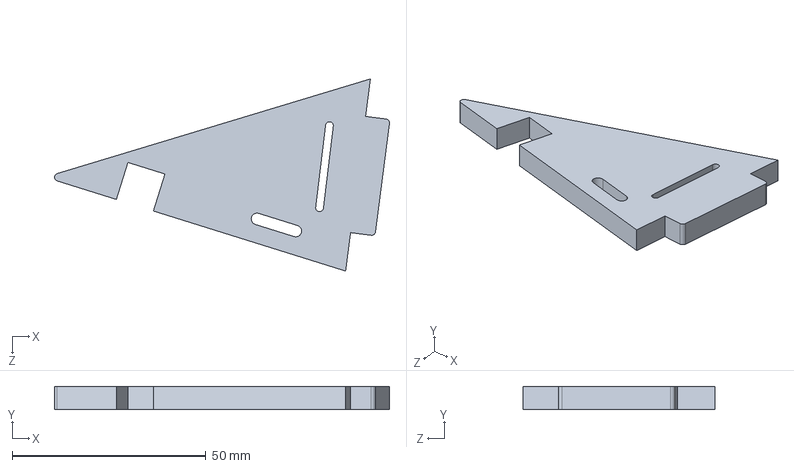
[picture p95: CAD file, 2023-05-31]
Module 4/surface_p3.SLDPRT
86.5 x 6.00 x 49.6 mm
