Jimmy-Chu-127/Pinball-Machine-Built-from-Scratch/Module 1/HC/ECE 115 Module 1 part2 HC.SLDPRT

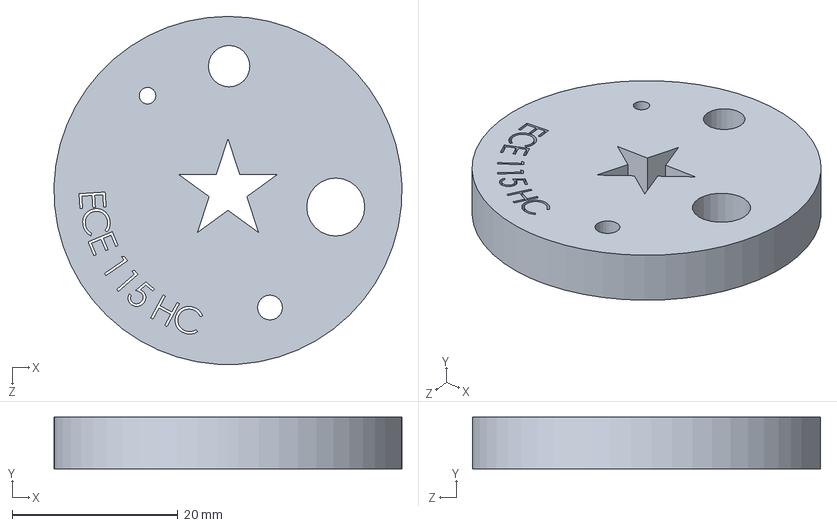
[picture p97: CAD file, 2023-04-07]
Module 1/HC/ECE 115 Module 1 part2 HC.SLDPRT
42.0 x 6.25 x 42.0 mm
