Jimmy-Chu-127/Pinball-Machine-Built-from-Scratch/Module 2 revision/slingshot cover large.SLDPRT

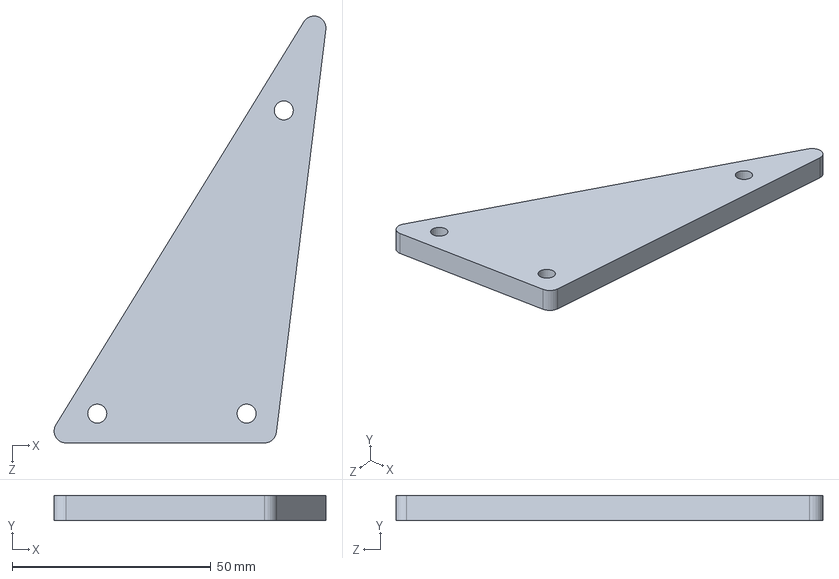
[picture p98: CAD file, 2023-05-23]
Module 2 revision/slingshot cover large.SLDPRT
68.4 x 6.35 x 107.5 mm
