Jimmy-Chu-127/Pinball-Machine-Built-from-Scratch/Module 2/slingshot arm.SLDPRT

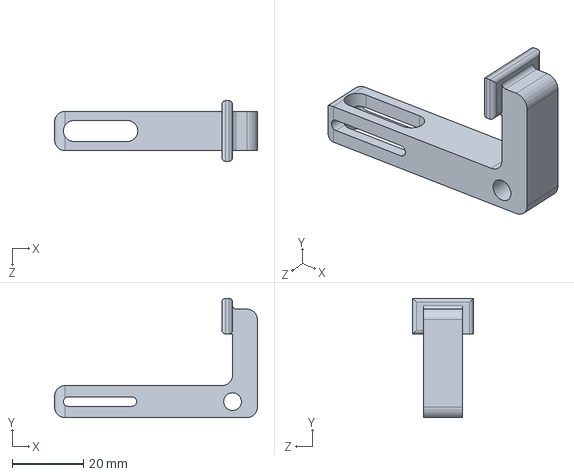
[picture p99: CAD file, 2023-05-12]
Module 2/slingshot arm.SLDPRT
57.0 x 33.5 x 17.0 mm
