Jimmy-Chu-127/Pinball-Machine-Built-from-Scratch/Module 4/flipper_button.SLDPRT

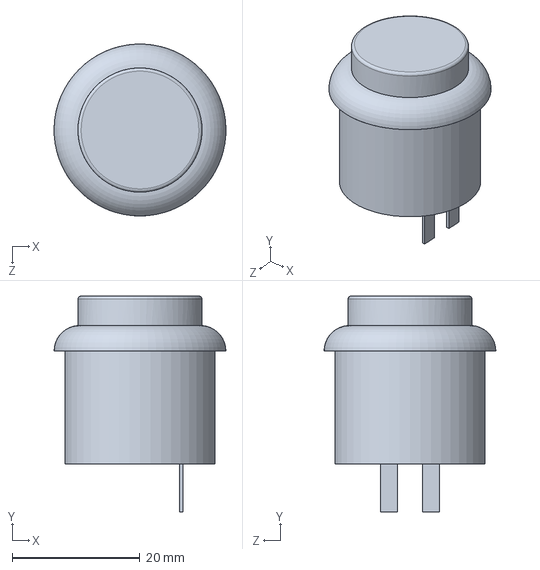
[picture p100: CAD file, 2023-05-24]
Module 4/flipper_button.SLDPRT
26.9 x 33.8 x 26.9 mm
