Jimmy-Chu-127/Pinball-Machine-Built-from-Scratch/Module 4/flipper_update/playfield.SLDPRT

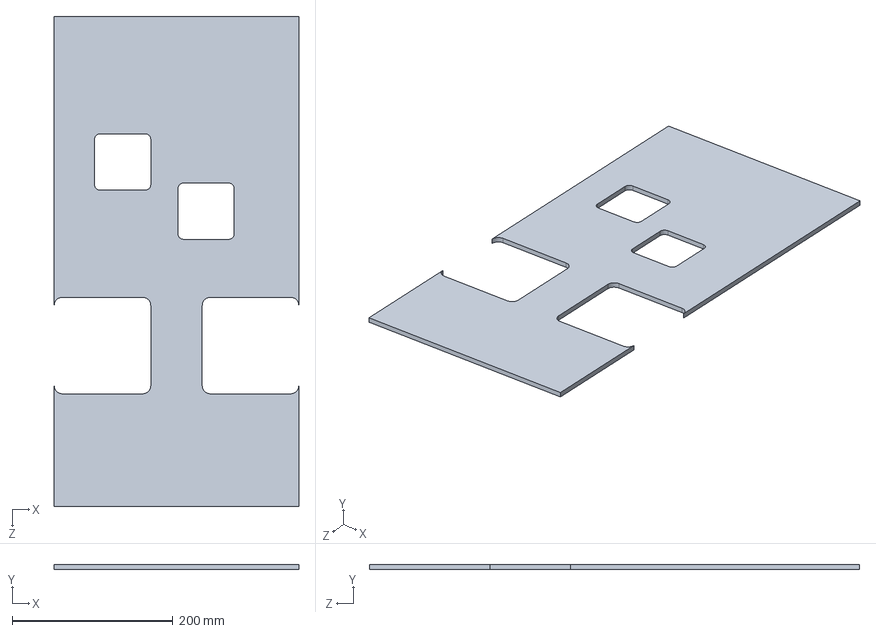
[picture p101: CAD file, 2023-05-14]
Module 4/flipper_update/playfield.SLDPRT
304.0 x 6.35 x 609.0 mm
