Jimmy-Chu-127/Pinball-Machine-Built-from-Scratch/Module 4/plunger_update/ECE 115 Module 1 plunger testbed side HC v2.SLDPRT

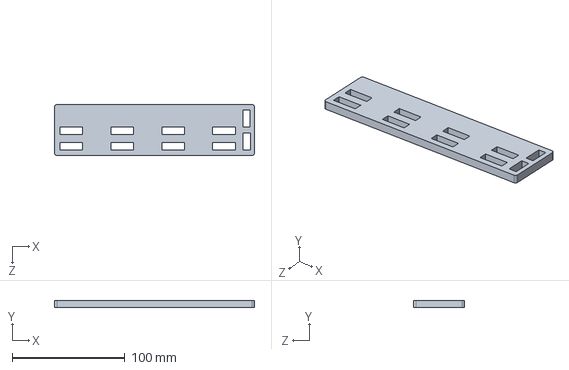
[picture p102: CAD file, 2023-04-12]
Module 4/plunger_update/ECE 115 Module 1 plunger testbed side HC v2.SLDPRT
177.0 x 6.35 x 45.0 mm
