Jimmy-Chu-127/Pinball-Machine-Built-from-Scratch/Module 2 revision/slingshot arm large.SLDPRT

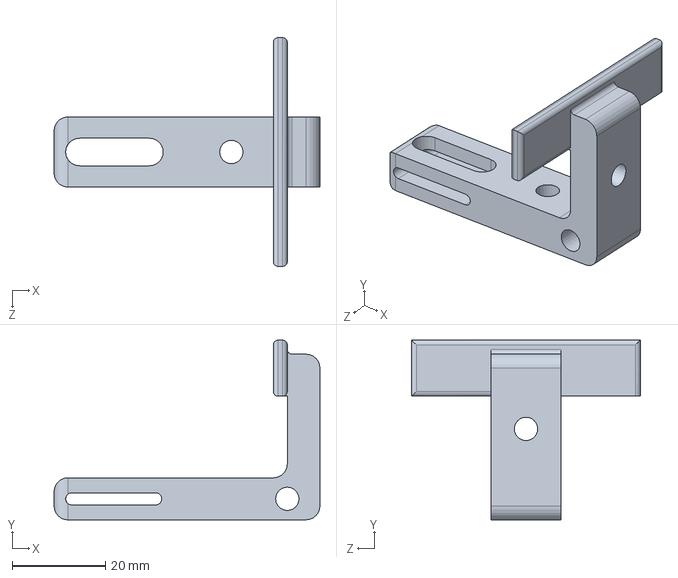
[picture p104: CAD file, 2023-05-23]
Module 2 revision/slingshot arm large.SLDPRT
57.0 x 38.5 x 49.0 mm
