Jimmy-Chu-127/Pinball-Machine-Built-from-Scratch/Module 2/slingshot testbed v2.SLDPRT

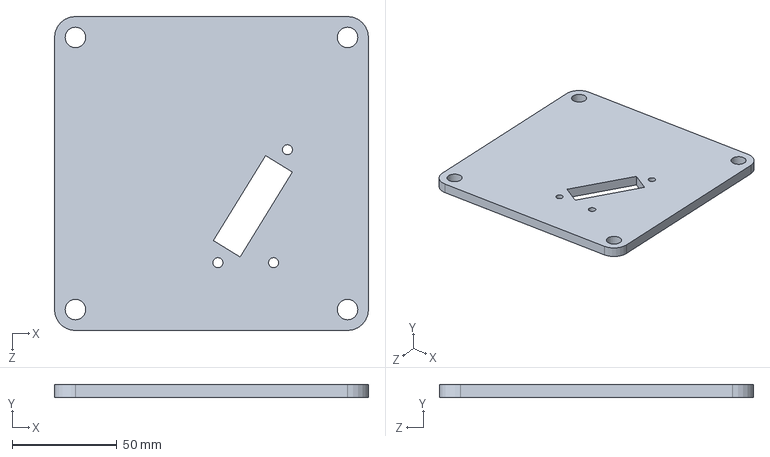
[picture p105: CAD file, 2023-05-12]
Module 2/slingshot testbed v2.SLDPRT
150.0 x 6.35 x 150.0 mm
