Jimmy-Chu-127/Pinball-Machine-Built-from-Scratch/Module 4/flipper_update/flipper_support_2.SLDPRT

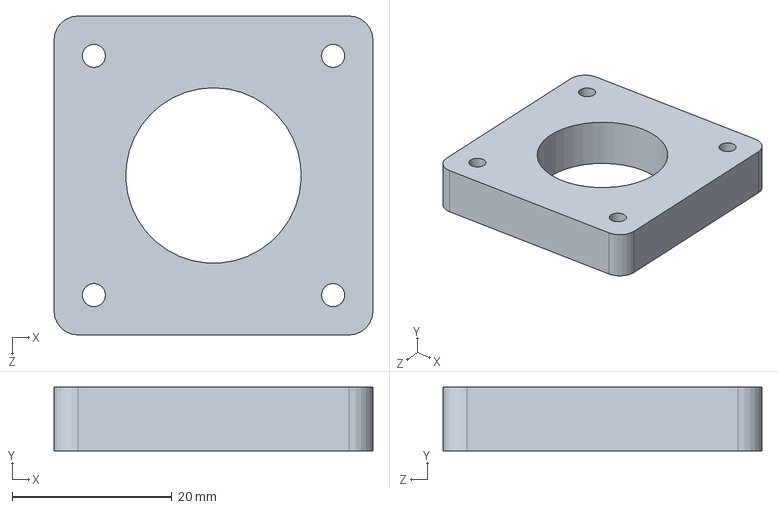
[picture p106: CAD file, 2023-05-14]
Module 4/flipper_update/flipper_support_2.SLDPRT
40.0 x 8.00 x 40.0 mm
