Jimmy-Chu-127/Pinball-Machine-Built-from-Scratch/Module 4/playfield v2.SLDPRT

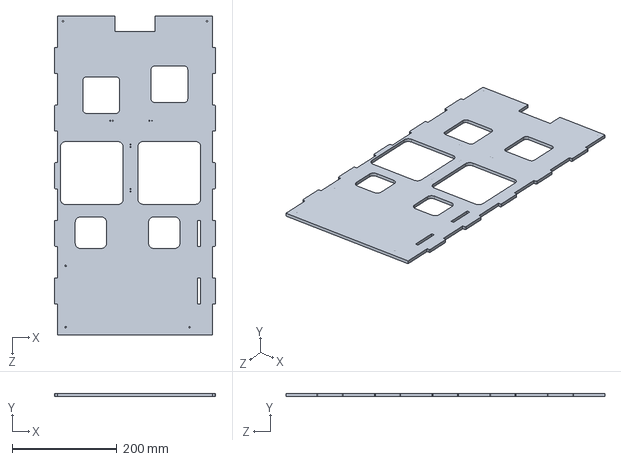
[picture p107: CAD file, 2023-05-24]
Module 4/playfield v2.SLDPRT
307.7 x 6.35 x 609.0 mm
