Jimmy-Chu-127/Pinball-Machine-Built-from-Scratch/3D printer - Laser cutting/5_24_cut/DXF/surface_p2.DXF

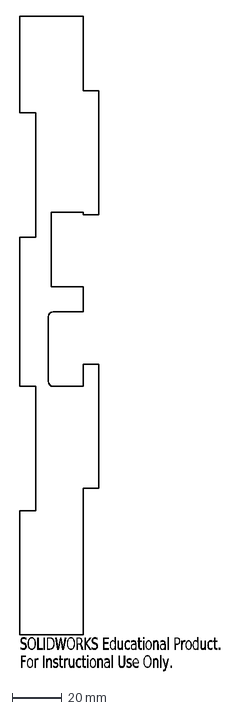
[picture p108: CAD file, 2023-05-24]
3D printer - Laser cutting/5_24_cut/DXF/surface_p2.DXF
SOLIDWORKS Educational Product.
For Instructional Use Only.
