Jimmy-Chu-127/Pinball-Machine-Built-from-Scratch/Module 2 revision/slingshot solenoid rod large.SLDPRT

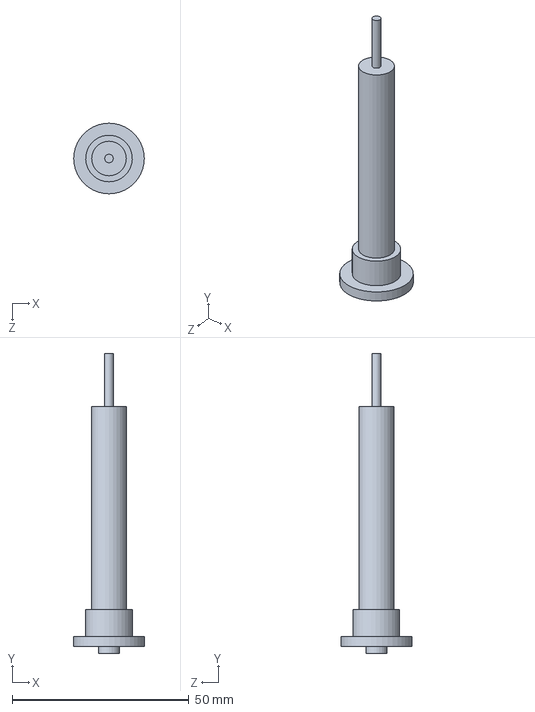
[picture p109: CAD file, 2023-05-23]
Module 2 revision/slingshot solenoid rod large.SLDPRT
20.0 x 84.9 x 20.0 mm
