Jimmy-Chu-127/Pinball-Machine-Built-from-Scratch/Module 2/slingshot solenoid rod.SLDPRT

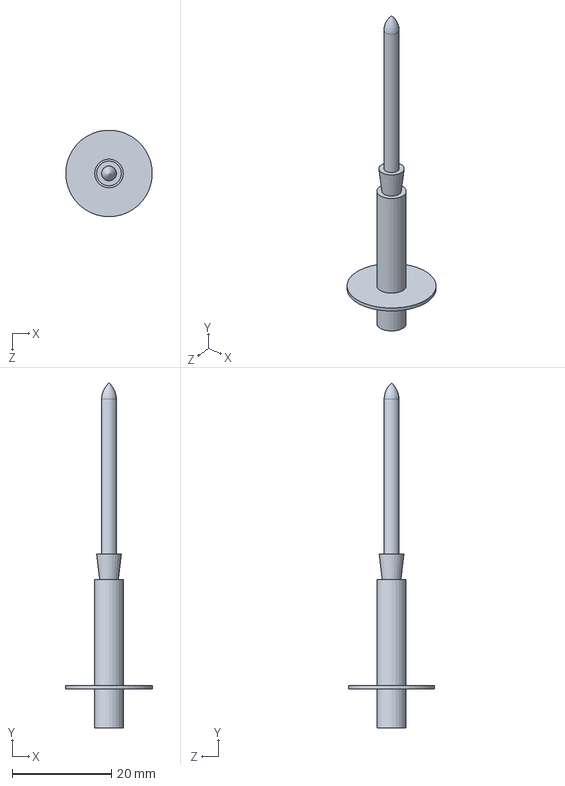
[picture p110: CAD file, 2023-05-12]
Module 2/slingshot solenoid rod.SLDPRT
17.5 x 69.6 x 17.4 mm
