Jimmy-Chu-127/Pinball-Machine-Built-from-Scratch/Module 4/flipper_update/solenoid_holder.SLDPRT

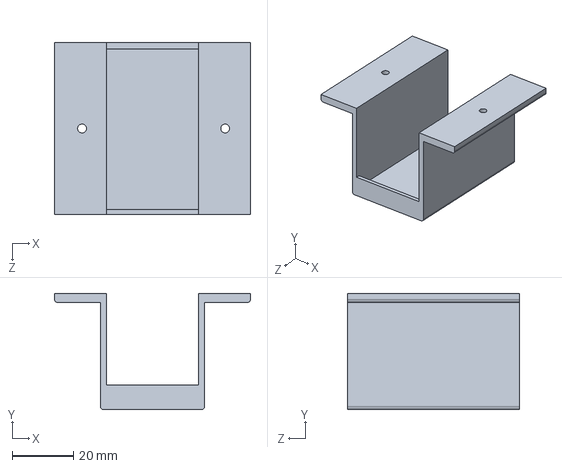
[picture p111: CAD file, 2023-05-14]
Module 4/flipper_update/solenoid_holder.SLDPRT
64.0 x 38.0 x 56.0 mm
