Jimmy-Chu-127/Pinball-Machine-Built-from-Scratch/Module 4/plunger_update/ECE 115 Module 1 plunger testbed right HC.SLDPRT

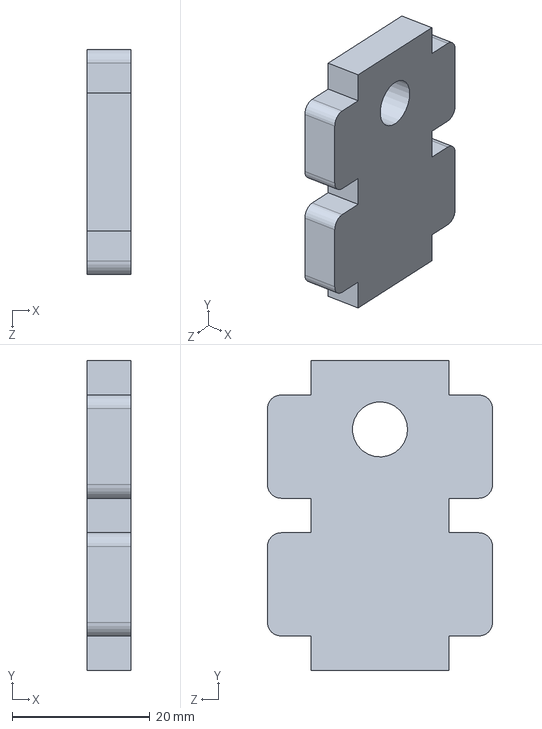
[picture p112: CAD file, 2023-04-09]
Module 4/plunger_update/ECE 115 Module 1 plunger testbed right HC.SLDPRT
6.35 x 45.0 x 32.7 mm
