Jimmy-Chu-127/Pinball-Machine-Built-from-Scratch/Module 4/surface_left_side_panel.SLDPRT

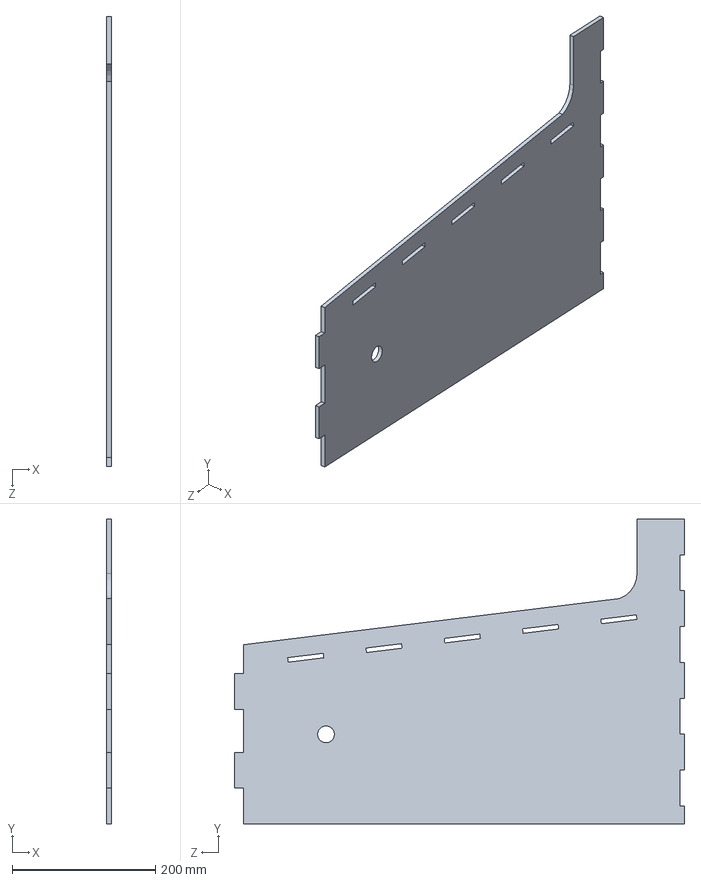
[picture p113: CAD file, 2023-05-24]
Module 4/surface_left_side_panel.SLDPRT
6.35 x 425.3 x 627.7 mm
