Jimmy-Chu-127/Pinball-Machine-Built-from-Scratch/Module 2 revision/slingshot solenoid body large.SLDPRT

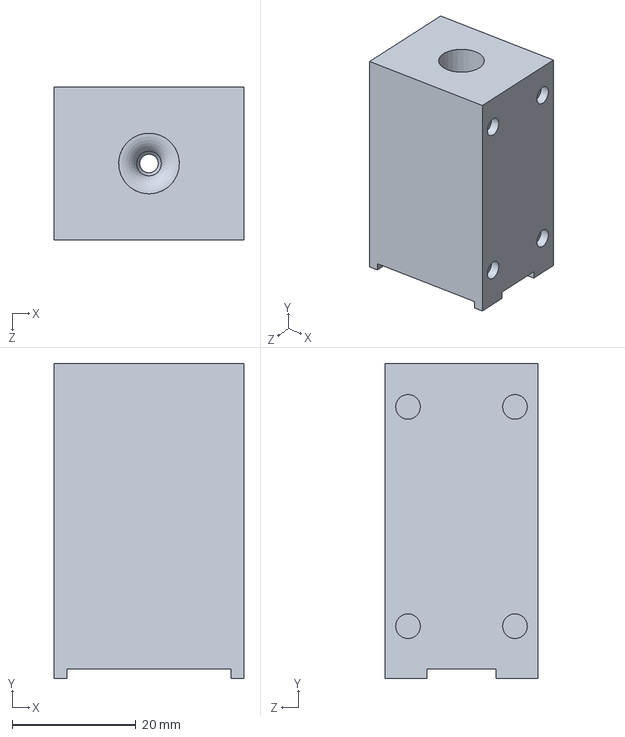
[picture p114: CAD file, 2023-05-23]
Module 2 revision/slingshot solenoid body large.SLDPRT
30.6 x 50.8 x 24.7 mm
