Jimmy-Chu-127/Pinball-Machine-Built-from-Scratch/Module 2/slingshot solenoid holder vertical.SLDPRT

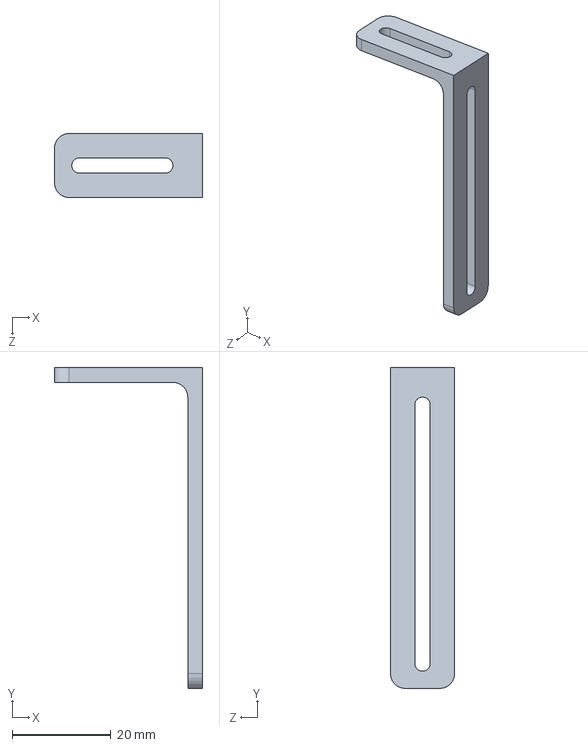
[picture p115: CAD file, 2023-05-07]
Module 2/slingshot solenoid holder vertical.SLDPRT
30.0 x 65.0 x 13.0 mm
