Jimmy-Chu-127/Pinball-Machine-Built-from-Scratch/Module 4/plunger_update/ECE 115 Module 1 plunger testbed base HC.SLDPRT

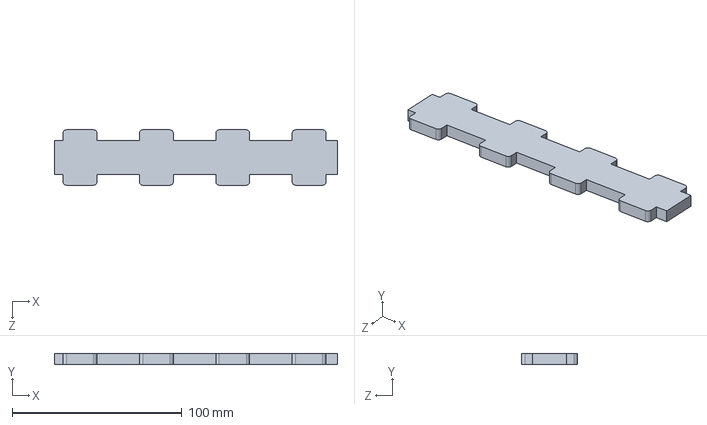
[picture p117: CAD file, 2023-04-09]
Module 4/plunger_update/ECE 115 Module 1 plunger testbed base HC.SLDPRT
166.7 x 6.35 x 32.7 mm
