Jimmy-Chu-127/Pinball-Machine-Built-from-Scratch/Module 2 revision/slingshot support rod large.SLDPRT

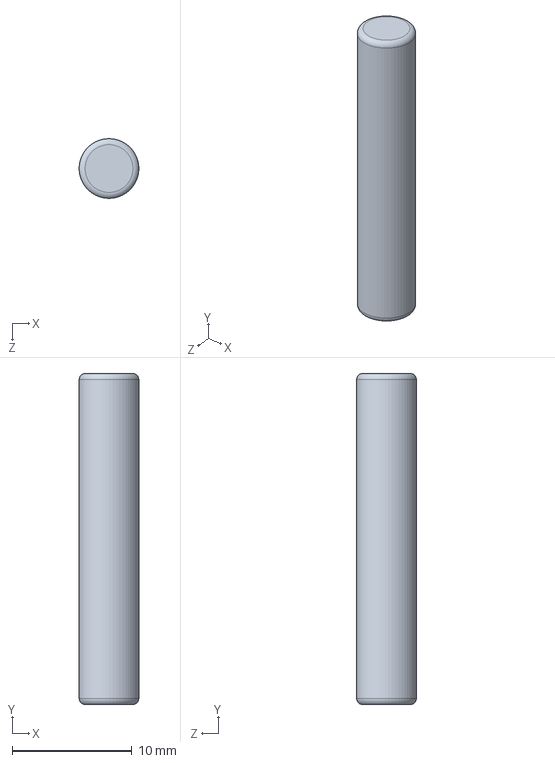
[picture p119: CAD file, 2023-05-23]
Module 2 revision/slingshot support rod large.SLDPRT
4.99 x 27.7 x 5.00 mm
