Jimmy-Chu-127/Pinball-Machine-Built-from-Scratch/Module 2/slingshot arm rotate rod.SLDPRT

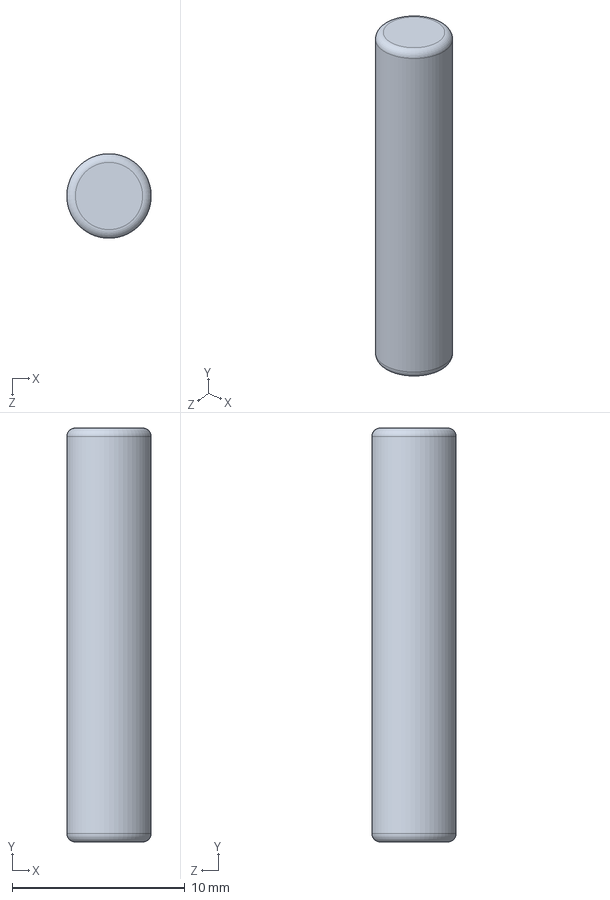
[picture p120: CAD file, 2023-05-07]
Module 2/slingshot arm rotate rod.SLDPRT
4.90 x 24.0 x 4.90 mm
