Jimmy-Chu-127/Pinball-Machine-Built-from-Scratch/Module 4/flipper_update/flipper_part3.SLDPRT

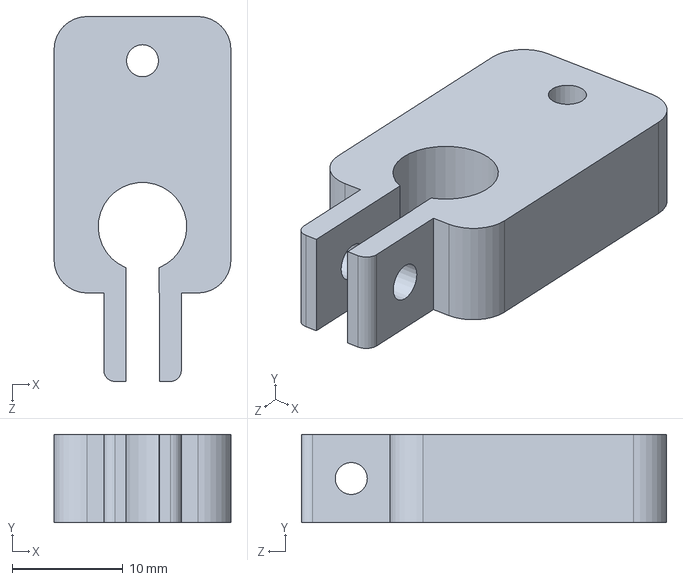
[picture p121: CAD file, 2023-04-25]
Module 4/flipper_update/flipper_part3.SLDPRT
16.0 x 8.00 x 33.0 mm
