Jimmy-Chu-127/Pinball-Machine-Built-from-Scratch/Module 4/surface_p5.SLDPRT

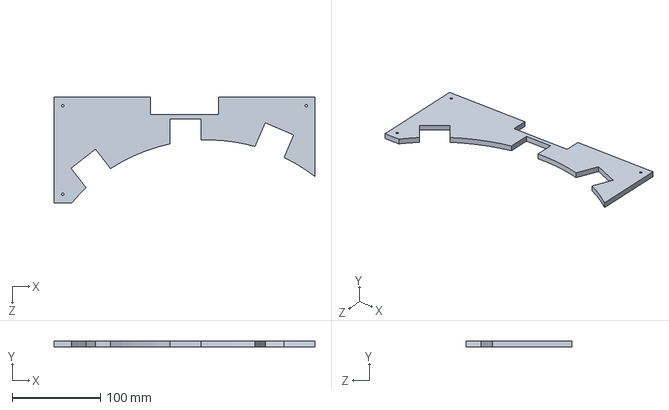
[picture p122: CAD file, 2023-05-24]
Module 4/surface_p5.SLDPRT
295.0 x 6.35 x 120.0 mm
