Jimmy-Chu-127/Pinball-Machine-Built-from-Scratch/Module 2 revision/slingshot rotate locker.SLDPRT

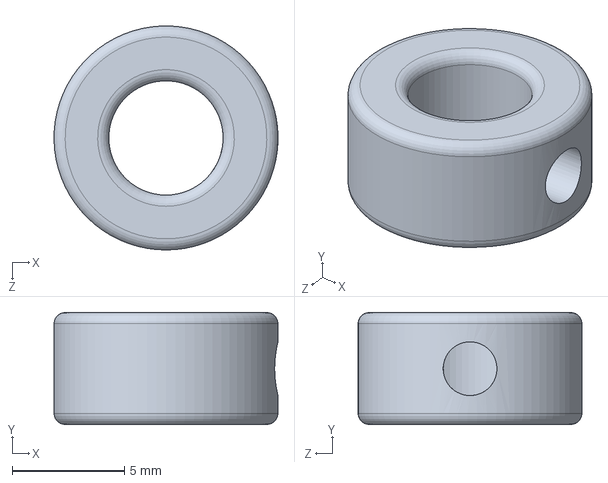
[picture p123: CAD file, 2023-05-23]
Module 2 revision/slingshot rotate locker.SLDPRT
10.00 x 5.00 x 10.00 mm
