Jimmy-Chu-127/Pinball-Machine-Built-from-Scratch/Module 2/slingshot solenoid body.SLDPRT

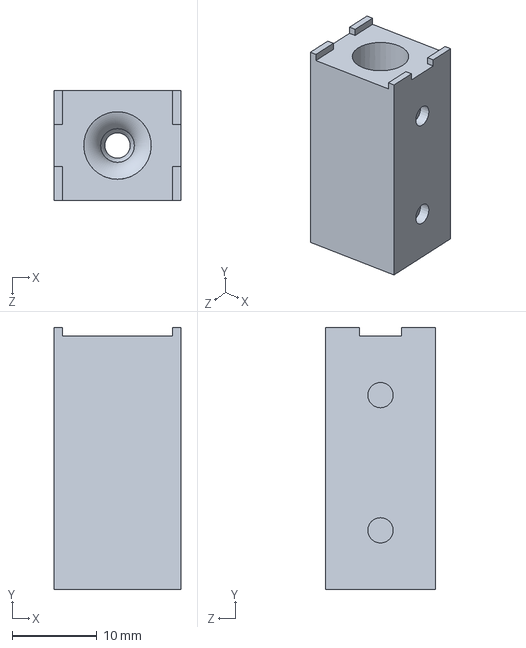
[picture p124: CAD file, 2023-05-07]
Module 2/slingshot solenoid body.SLDPRT
15.0 x 31.0 x 13.0 mm
