Jimmy-Chu-127/Pinball-Machine-Built-from-Scratch/Module 4/_A6LM-M14G_round.SLDPRT

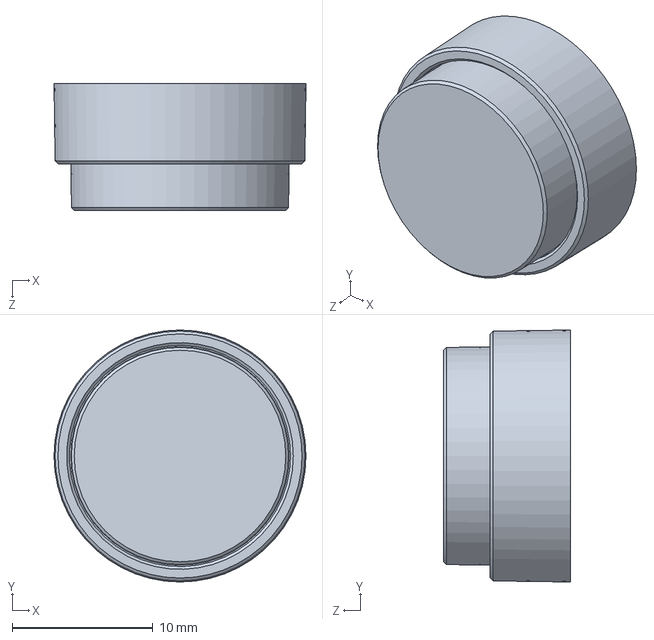
[picture p125: CAD file, 2023-05-24]
Module 4/_A6LM-M14G_round.SLDPRT
17.9 x 17.9 x 9.00 mm
