Jimmy-Chu-127/Pinball-Machine-Built-from-Scratch/Module 4/flipper_update/flipper_bearing.SLDPRT

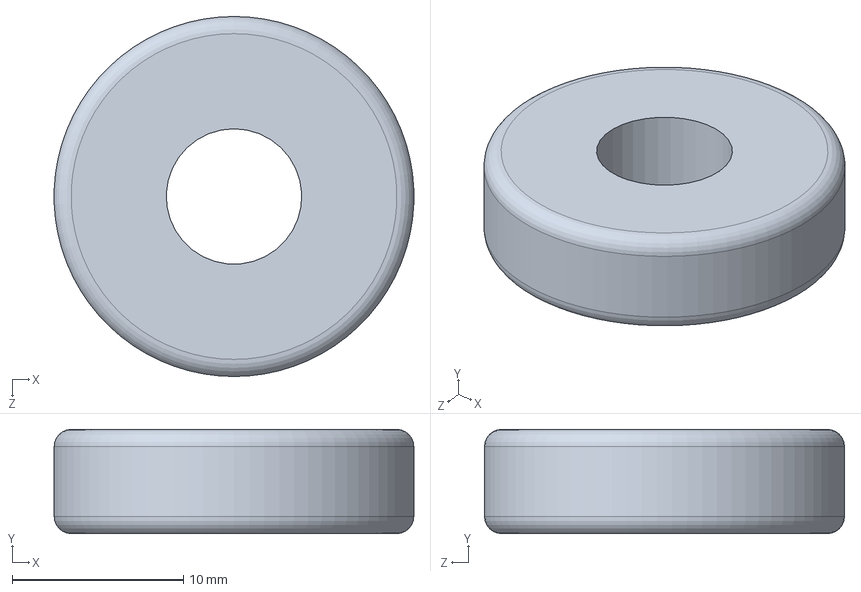
[picture p126: CAD file, 2023-04-20]
Module 4/flipper_update/flipper_bearing.SLDPRT
21.0 x 6.08 x 21.0 mm
