Jimmy-Chu-127/Pinball-Machine-Built-from-Scratch/Module 2 revision/slingshot solenoid holder vertical large.SLDPRT

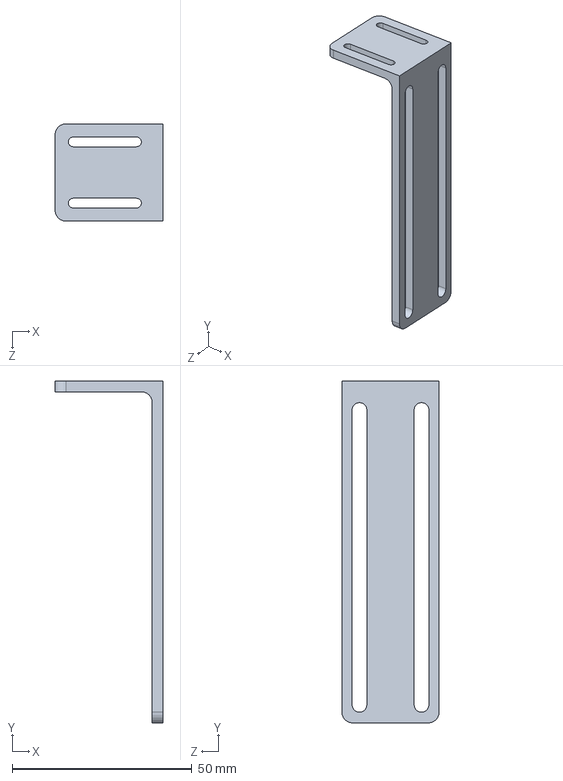
[picture p127: CAD file, 2023-05-23]
Module 2 revision/slingshot solenoid holder vertical large.SLDPRT
30.0 x 95.0 x 27.0 mm
