Jimmy-Chu-127/Pinball-Machine-Built-from-Scratch/Module 2/slingshot limit switch.SLDPRT

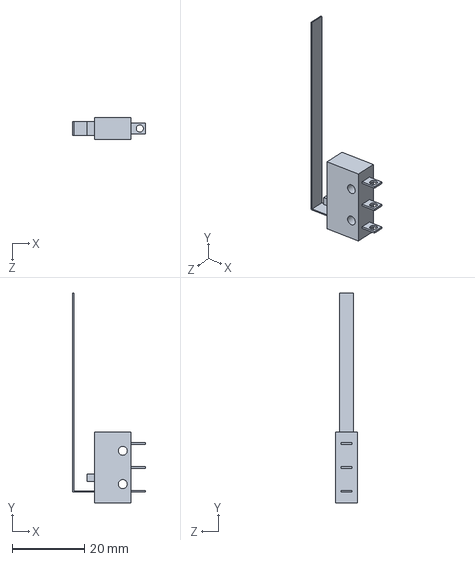
[picture p128: CAD file, 2023-05-07]
Module 2/slingshot limit switch.SLDPRT
20.1 x 58.3 x 6.20 mm
