Jimmy-Chu-127/Pinball-Machine-Built-from-Scratch/Module 4/flipper_update/flipper_part4.SLDPRT

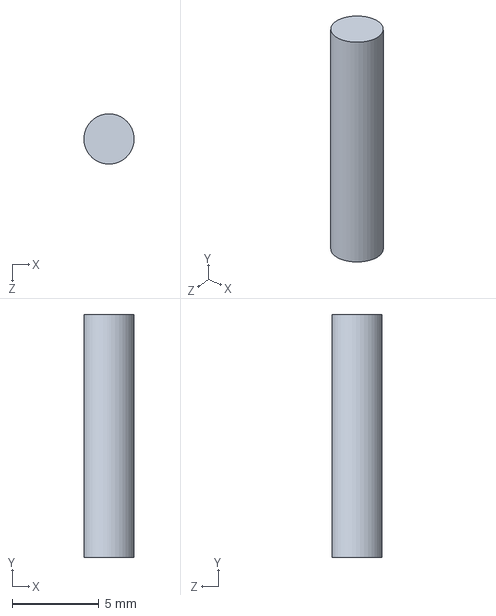
[picture p129: CAD file, 2023-04-20]
Module 4/flipper_update/flipper_part4.SLDPRT
2.90 x 14.0 x 2.90 mm
