Jimmy-Chu-127/Pinball-Machine-Built-from-Scratch/Module 2 revision/slingshot solenoid tail connector with insert.SLDPRT

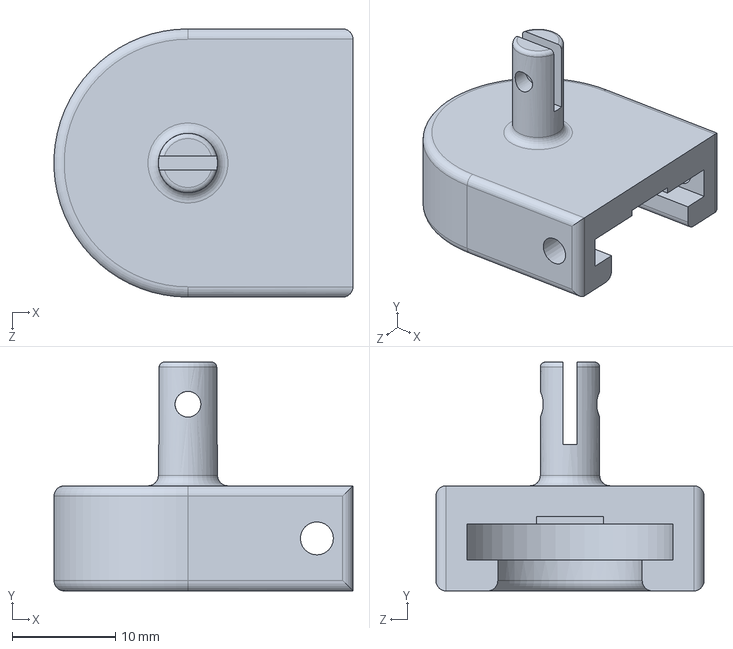
[picture p130: CAD file, 2023-05-23]
Module 2 revision/slingshot solenoid tail connector with insert.SLDPRT
29.0 x 22.2 x 26.0 mm
