Jimmy-Chu-127/Pinball-Machine-Built-from-Scratch/Module 2/slingshot limit switch holder.SLDPRT

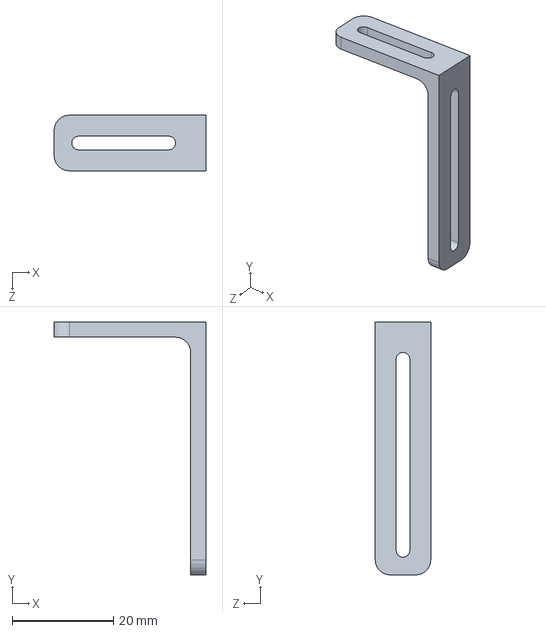
[picture p131: CAD file, 2023-05-07]
Module 2/slingshot limit switch holder.SLDPRT
30.0 x 50.0 x 11.0 mm
