Jimmy-Chu-127/Pinball-Machine-Built-from-Scratch/Module 2 revision/slingshot testbed v4.DXF

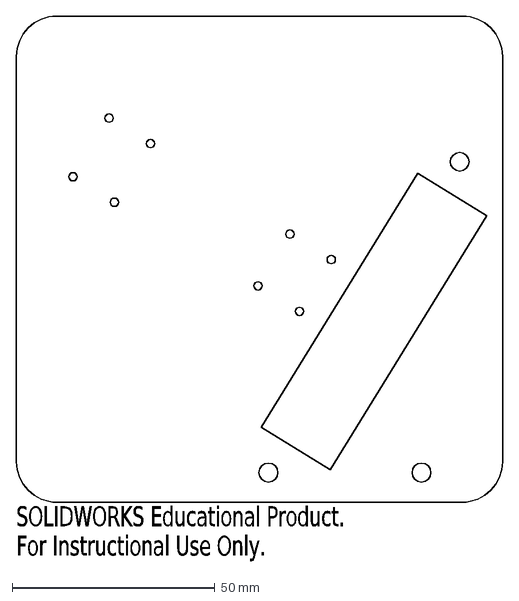
[picture p132: CAD file, 2023-05-17]
Module 2 revision/slingshot testbed v4.DXF
SOLIDWORKS Educational Product.
For Instructional Use Only.
