Jimmy-Chu-127/Pinball-Machine-Built-from-Scratch/Module 2/slingshot testbed support rod.SLDPRT

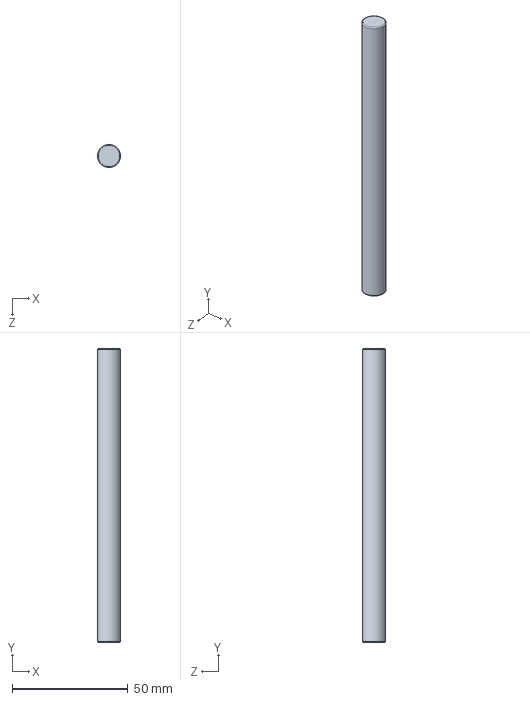
[picture p133: CAD file, 2023-05-07]
Module 2/slingshot testbed support rod.SLDPRT
9.98 x 127.0 x 10.0 mm
