Jimmy-Chu-127/Pinball-Machine-Built-from-Scratch/Module 4/flipper_update/flipper_part2.SLDPRT

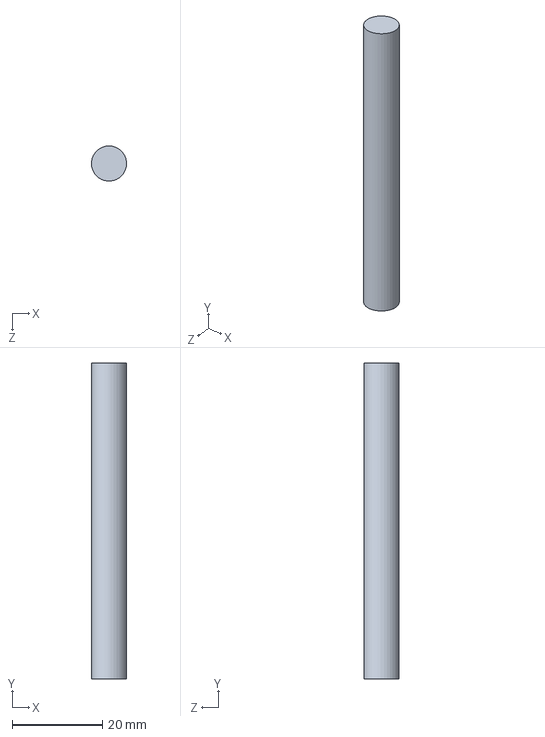
[picture p134: CAD file, 2023-04-20]
Module 4/flipper_update/flipper_part2.SLDPRT
7.79 x 70.0 x 7.80 mm
