Jimmy-Chu-127/Pinball-Machine-Built-from-Scratch/Module 2 revision/slingshot part set.3mf

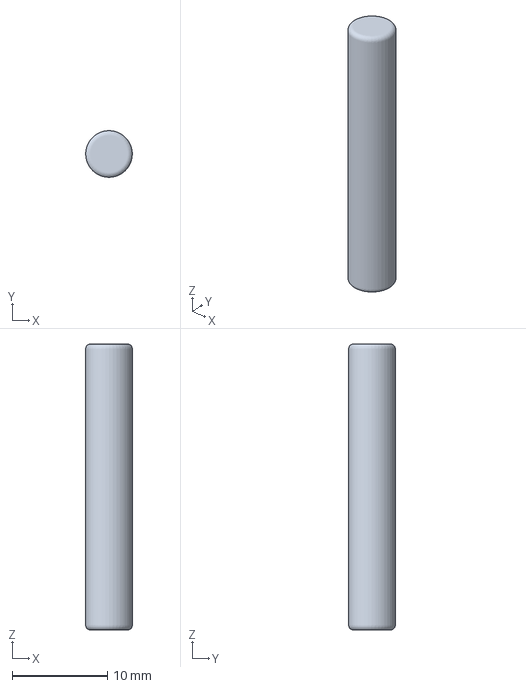
[picture p135: CAD file, 2023-05-17]
Module 2 revision/slingshot part set.3mf
4.90 x 4.90 x 30.0 mm
