Jimmy-Chu-127/Pinball-Machine-Built-from-Scratch/Module 2/slingshot cover.SLDPRT

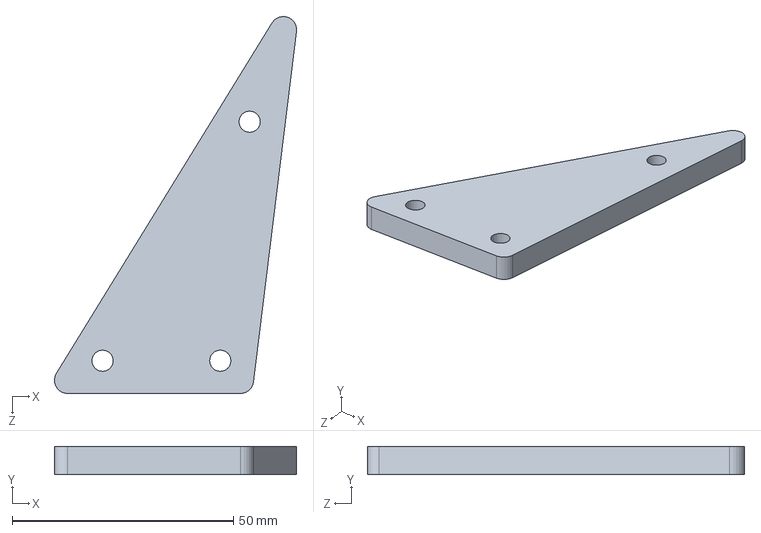
[picture p136: CAD file, 2023-05-07]
Module 2/slingshot cover.SLDPRT
54.7 x 6.35 x 85.1 mm
