Jimmy-Chu-127/Pinball-Machine-Built-from-Scratch/Module 4/surface_front_panel.SLDPRT

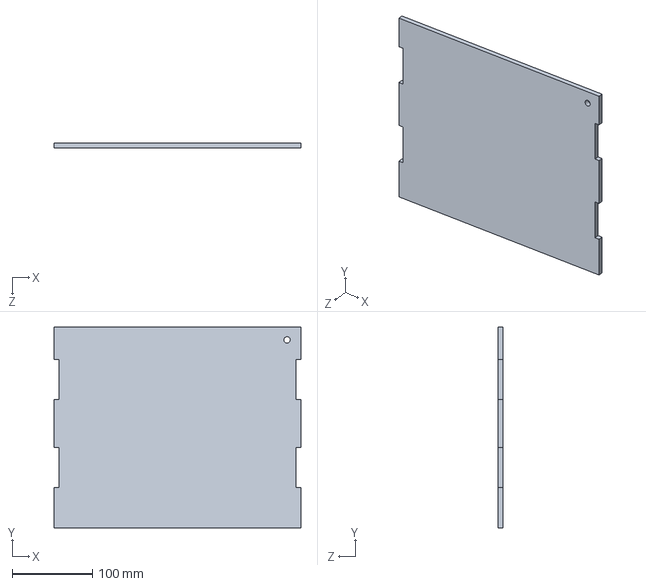
[picture p137: CAD file, 2023-05-23]
Module 4/surface_front_panel.SLDPRT
307.7 x 250.0 x 6.35 mm
