Jimmy-Chu-127/Pinball-Machine-Built-from-Scratch/Module 4/surface_plunger_cover.SLDPRT

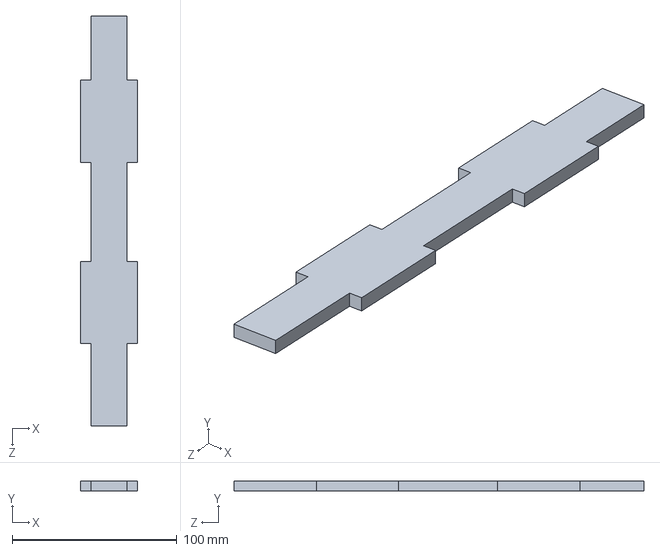
[picture p138: CAD file, 2023-05-22]
Module 4/surface_plunger_cover.SLDPRT
34.7 x 6.35 x 249.0 mm
