Jimmy-Chu-127/Pinball-Machine-Built-from-Scratch/Module 2 revision/slingshot fit tester.DXF

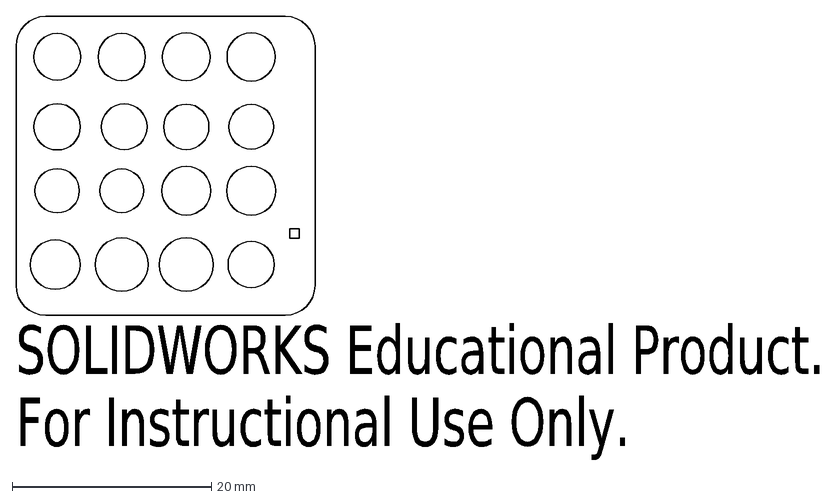
[picture p139: CAD file, 2023-05-13]
Module 2 revision/slingshot fit tester.DXF
SOLIDWORKS Educational Product.
For Instructional Use Only.
