Jimmy-Chu-127/Pinball-Machine-Built-from-Scratch/Module 2/slingshot solenoid_holder.SLDPRT

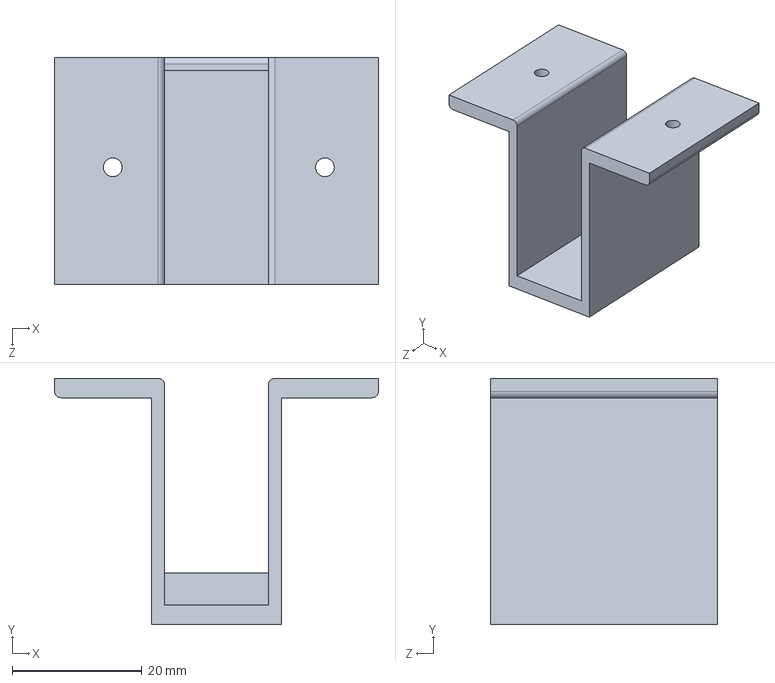
[picture p140: CAD file, 2023-04-26]
Module 2/slingshot solenoid_holder.SLDPRT
50.0 x 38.0 x 35.0 mm
