Jimmy-Chu-127/Pinball-Machine-Built-from-Scratch/Module 4/surface_connector.SLDPRT

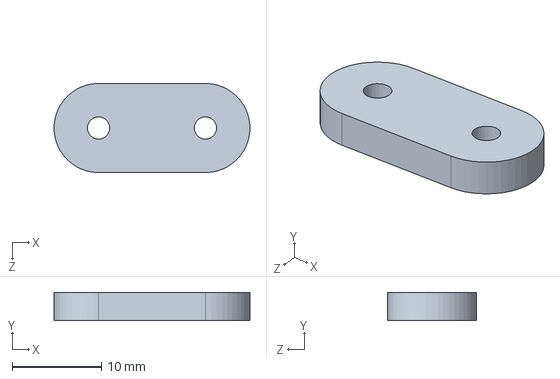
[picture p141: CAD file, 2023-05-21]
Module 4/surface_connector.SLDPRT
22.0 x 3.18 x 10.0 mm
