Jimmy-Chu-127/Pinball-Machine-Built-from-Scratch/Module 2/flipper_part5.SLDPRT

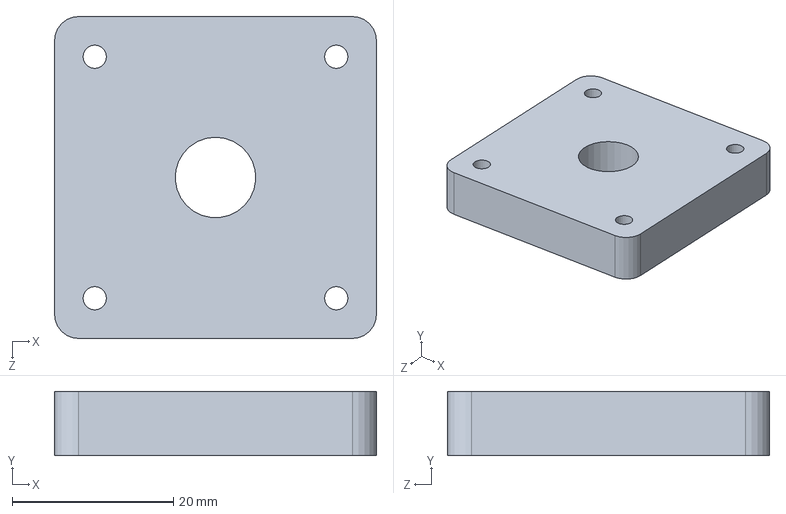
[picture p142: CAD file, 2023-04-25]
Module 2/flipper_part5.SLDPRT
40.0 x 8.00 x 40.0 mm
