Jimmy-Chu-127/Pinball-Machine-Built-from-Scratch/Module 4/servo.SLDPRT

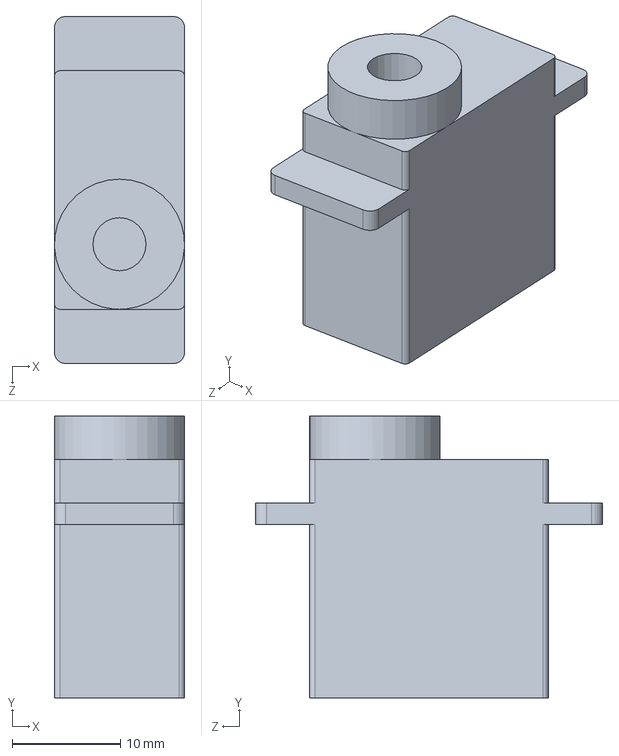
[picture p143: CAD file, 2023-05-18]
Module 4/servo.SLDPRT
12.0 x 26.0 x 32.0 mm
