Jimmy-Chu-127/Pinball-Machine-Built-from-Scratch/Module 4/surface_p4.SLDPRT

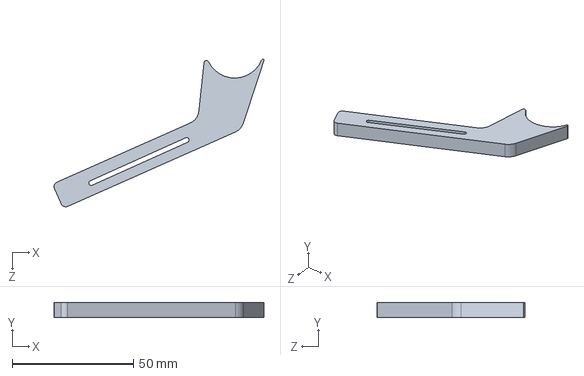
[picture p144: CAD file, 2023-05-18]
Module 4/surface_p4.SLDPRT
86.6 x 6.35 x 60.9 mm
