Jimmy-Chu-127/Pinball-Machine-Built-from-Scratch/Module 2/plane.SLDPRT

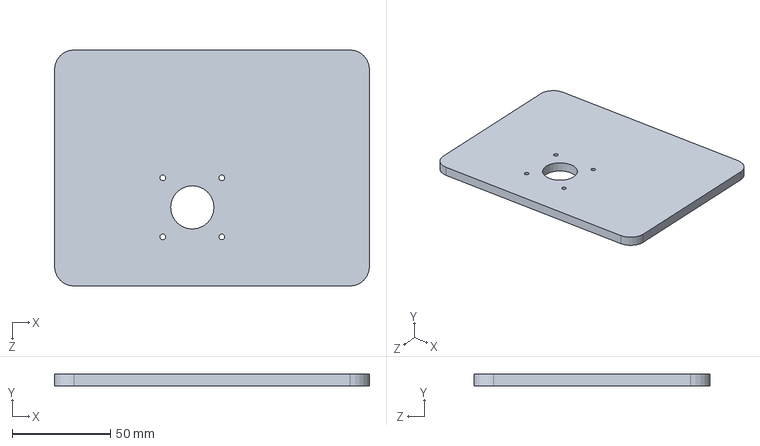
[picture p145: CAD file, 2023-04-25]
Module 2/plane.SLDPRT
160.0 x 5.90 x 120.0 mm
