Jimmy-Chu-127/Pinball-Machine-Built-from-Scratch/Module 2/ECE 115 spin wheel holder side.SLDPRT

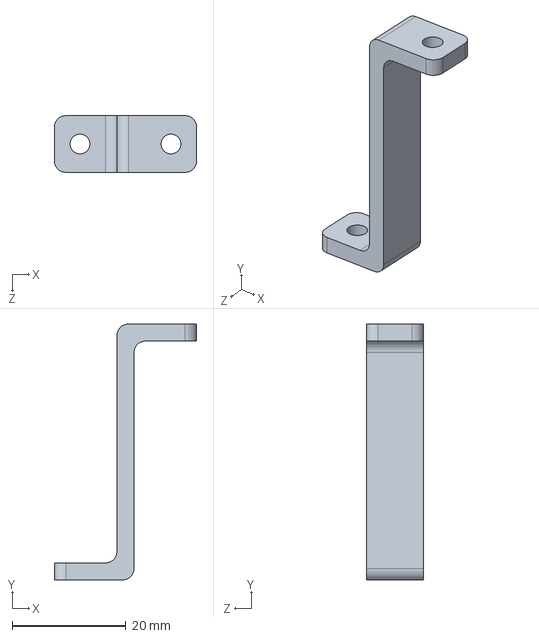
[picture p146: CAD file, 2023-04-21]
Module 2/ECE 115 spin wheel holder side.SLDPRT
25.0 x 45.0 x 10.0 mm
