Jimmy-Chu-127/Pinball-Machine-Built-from-Scratch/Module 2/ECE 115 spin wheel rod.SLDPRT

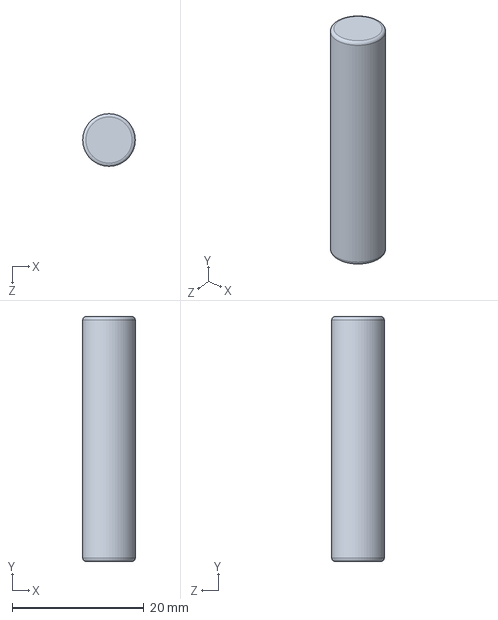
[picture p147: CAD file, 2023-04-21]
Module 2/ECE 115 spin wheel rod.SLDPRT
8.00 x 37.2 x 8.00 mm
