Jimmy-Chu-127/Pinball-Machine-Built-from-Scratch/Module 2/ECE 115 DC motor geared.SLDPRT

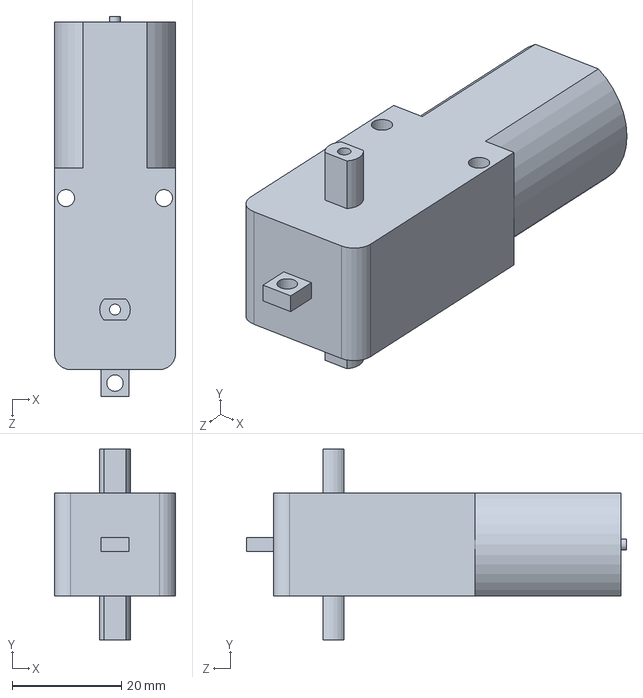
[picture p148: CAD file, 2023-04-21]
Module 2/ECE 115 DC motor geared.SLDPRT
22.2 x 34.9 x 69.5 mm
