Jimmy-Chu-127/Pinball-Machine-Built-from-Scratch/Module 5/pinball_machine_fsm/power_system.ino

int powerButtonPin = 30;

void setupPower(){
  pinMode(powerButtonPin, INPUT);
}

int powerButtonOn(){
  //Serial.println("Power: " + String(digitalRead(powerButtonPin)));
  return digitalRead(powerButtonPin); //check if the system is turned on
}
